ibukeev/cat_bike/docs/design/photo-layout-analysis.md

# Photo Layout Analysis

## Purpose

Use the front/back bike photos as the baseline for LED placement, mechanical clearance, and future sculptural planning.

## Photo Reference Map

| Photo | Best Use |
|---|---|
| [01-bike-front-straight.jpg](../../assets/photos/Original_bike/front_back/01-bike-front-straight.jpg) | Front symmetry, fork clearance, tire/headlight alignment, handlebar width. |
| [02-bike-side-profile-wide.jpg](../../assets/photos/Original_bike/front_back/02-bike-side-profile-wide.jpg) | Whole-bike side layout, frame tube runs, battery clearance, pedal/chain clearance. |
| [03-bike-rear-rack-left-closeup.jpg](../../assets/photos/Original_bike/front_back/03-bike-rear-rack-left-closeup.jpg) | Rear rack, basket attachment, left-side tail mount options. |
| [04-bike-rear-straight.jpg](../../assets/photos/Original_bike/front_back/04-bike-rear-straight.jpg) | Rear visibility, tail symmetry, basket rear face, rear tire clearance. |
| [05-bike-side-profile-close.jpg](../../assets/photos/Original_bike/front_back/05-bike-side-profile-close.jpg) | Main side-frame LED routes and panel candidate zones. |
| [06-bike-rear-three-quarter-close.jpg](../../assets/photos/Original_bike/front_back/06-bike-rear-three-quarter-close.jpg) | Rear rack, basket side, tail path, rear wiring path. |
| [07-bike-rear-three-quarter-wide.jpg](../../assets/photos/Original_bike/front_back/07-bike-rear-three-quarter-wide.jpg) | Whole-bike rear/side silhouette and visibility from distance. |
| [08-bike-front-top-handlebar-head-tube.jpg](../../assets/photos/Original_bike/front_back/08-bike-front-top-handlebar-head-tube.jpg) | Handlebar/head tube area, head mount envelope, brake cable and headlight clearance. |

## First-Pass Layout Annotations

### Front Area

- The existing front headlight sits low and forward; do not block it unless it is intentionally replaced.
- The handlebar and head tube area are crowded with brake cables and controls, so the cat head should either mount to a dedicated bracket or use a carefully placed handlebar/stem clamp.
- Front fork lighting can run down the fork legs, but must stay clear of the tire, brake rotor, and cable motion.
- The cat head should be removable and should have a service connector near the head tube or stem.

### Side Frame

- The lower frame tube is the strongest candidate for Phase 1 underglow because it is independent of future sculptural panels.
- The large battery occupies the central frame area; do not block battery removal, key access, or charging access.
- The step-through frame creates a good visible side silhouette, but panel work should remain removable.
- Pedal, chain, and kickstand clearance should be treated as no-go zones for wiring and panels.

### Rear Rack and Basket

- The rear rack and basket provide strong mounting structure for Phase 1 rear lighting.
- Basket perimeter lighting is useful for rear/side visibility and does not depend on body panels.
- Tail mounting should use the rack/basket structure, with a quick disconnect and a secondary safety tether.
- Tail design must preserve cargo use unless cargo is intentionally sacrificed for the event build.

### Body Panels

- Body panels should be treated as Phase 3 because LED placement may depend on the inside face of the panel.
- Phase 1 should reserve power/data connectors for future panel lighting instead of installing those LEDs early.
- Candidate panel zones are the side frame opening, rear rack side, and front lower frame/fork transition.

### Wheels

- Wheel effects remain Phase 4. They are visually strong but add durability, power, and maintenance complexity.
- Any wheel lighting must avoid spokes, brake rotors, tires, valve stems, and wheel removal/service.

## Phase 1 Reference Review

Current visual reference: [phase1-led-reference-v3-current.png](../../assets/photos/Concepts/Bio-Luminescent%20Abyssinian/Phase_1_LED_References/phase1-led-reference-v3-current.png)

What to keep:

- Restrained lower frame lighting with a segmented addressable feel.
- Short fork accents instead of full fork outlines.
- Rear rack support accents.
- Subtle hidden basket underside glow.
- Soft ground underglow.
- Cyan/aqua base palette with small violet/magenta pulse accents.
- Unlit flag post.

What to reject from earlier iterations:

- Wheel rings, tire lights, spoke lights, and wheel effects.
- Handlebar, grip, brake lever, or control-area lighting.
- Dense basket-face lighting or woven basket string lights.
- Random magenta dots not tied to a real endpoint or junction.
- Any literal geometry that cannot be mounted cleanly with removable, protected LED channels.

## Rough Reference Dimensions

These are planning references based on current RadRunner-family specifications and should be verified against Olga's actual bike before ordering parts or cutting materials.

| Dimension | Reference Value | Planning Use |
|---|---:|---|
| Total bike length | 68 in / 172.7 cm | Overall side layout and transport envelope. |
| Wheelbase | 45 in / 114.3 cm | Scales side-view estimates. |
| Handlebar width | 27 in / 68.6 cm | Front cat head maximum visual width reference. |
| Handlebar height | 42-45 in / 106.7-114 cm | Cat head height and rider sightline reference. |
| Tire size | 20 in x 3.3 in | Fork, wheel, and fender clearance reference. |
| Rear rack payload | 120 lb / 54.4 kg | Tail/rack sculpture load reference, though the sculpture should be far lighter. |

Sources:

- Rad Power Bikes product specs: https://www.radpowerbikes.com/collections/eligible-ebikes/products/radrunner-electric-cargo-utility-bike

## Phase 1 Candidate LED Runs

| Zone | Rough Length Estimate | Why It Belongs in Phase 1 |
|---|---:|---|
| Lower frame underglow | 30-45 in per side | Independent of panels, high visibility, protected if mounted inboard. |
| Fork legs | 18-24 in per fork leg | Improves front visibility; must be mechanically protected. |
| Rear rack perimeter | 40-70 in | Strong mounting structure and rear visibility. |
| Basket front/rear faces | 30-60 in total | High visibility, easy to mount, removable with basket work. |

## Reserved Interfaces

| Future Zone | Reserve Location | Notes |
|---|---|---|
| Cat head | Head tube/stem area | Needs power/data quick disconnect and strain relief. |
| Tail | Rear rack/basket area | Needs removable connector and safety tether route. |
| Body panels | Side frame and rear rack area | Wait for real panel geometry before installing LEDs. |
| Wheels | Near fork/rear triangle only if pursued | Defer until fixed lighting is stable. |

## Measurements Still Needed

- Actual lower frame tube LED path length.
- Fork leg usable straight length.
- Rear rack and basket dimensions.
- Basket hole spacing and usable clamp locations.
- Battery removal path and required clearance.
- Headlight beam envelope.
- Full steering sweep with cables.
- Tail mount envelope and cargo clearance.
