ibukeev/cat_bike/hardware/mechanical/fabrication/templates/cat-head-wireframe-prototype/gemini_3d_plus_symmetry_report.md

# Gemini 3D Plus Symmetry Model Report

This is a proof model generated from manual mappings plus accepted symmetry-derived points. It is not fabrication-ready CAD.

## Counts

- 3D nodes: 69
- Rods generated: 162
- Skipped projection edges: 31
- Heavy-estimate nodes: 30
- Heavy-estimate nodes in inferred back/deep half: 22
- manual 3-view trace: 17
- symmetry, traced mirror nodes: 4
- manual partial constraints: 14
- some estimated projection: 4
- heavily estimated: 30

## Fit Summary

- top_x_to_front_x: x = 1.082926 * top_x + -30.919
- top_y_to_side_depth: y = -0.862602 * top_y + 3133.149
- side_y_to_front_y: z_y = 1.005460 * side_y + -5.852

## Files

- `gemini-3d-plus-symmetry-wireframe.html`
- `gemini-3d-plus-symmetry-wireframe.obj`
- `gemini-3d-plus-symmetry-wireframe.stl`
- `gemini_3d_plus_symmetry_nodes.csv`
- `gemini_3d_plus_symmetry_rods.csv`
- `gemini_obj_part_map.csv`
- `gemini_3d_plus_symmetry_projection_residuals.csv`
- `gemini_3d_plus_symmetry_skipped_edges.csv`
- `gemini-3d-back-review-markers.obj`
- `gemini-3d-back-review-markers.mtl`
- `gemini_3d_back_review_nodes.csv`
