ibukeev/cat_bike/assets/photos/Concepts/Selected/Bio-Luminescent Abyssinian/Phase_1_LED_References/body-strip-design-options-v1/generation-prompts.md

# Regeneration prompt sequence

Use built-in `image_gen`. Begin with the corrected placement mockup as the only conversation image, then use each latest result as the sole input for the next option (`num_last_images_to_include: 1`). Preserve the real bicycle, geometry, background, and dusk treatment in every edit.

## Option 1 — Minimal Feline Silhouette

`Replace the existing LED routing with exactly three elements: one continuous cyan/teal lower-frame strip following the rear lower frame through the step-through belly curve; one continuous cyan/teal upper rear haunch strip beneath the seat/rack ending under the basket; and one short downward-facing basket-underlight. Remove vertical torso strips and accents. Keep generous dark negative space.`

## Option 2 — Bioluminescent Dashes

`Replace continuous strips with 7–9 short cyan/teal segments along the lower frame and belly curve, 4–5 separated segments along the upper rear haunch, one basket-underlight, and only two short magenta accents. Maintain consistent dark gaps and an organic animal-marking rhythm.`

## Option 3 — Feline Ribcage

`Remove the dashed outline. Add one cyan upper rear spine, four short diagonal cyan ribs on removable backing bars across the fixed rear-rack triangle, one short lower sternum/belly strip, one basket-underlight, and one small magenta heartbeat accent. Leave the front half mostly dark.`

## Option 4 — Geometric Facet Echo

`Remove the ribcage. Add 6–8 straight strip strokes: 4–5 forming two incomplete angular chevrons/open facets in the fixed rear-rack triangle, two short lower-frame strokes forming a shallow forward chevron, one basket-underlight, and one short magenta facet edge. Keep gaps at every corner; use no sharply bent continuous strip.`

## Invariants for every prompt

`No LEDs on forks, wheels, tires, spokes, brake rotors, chain, crank, steering components, cables, or moving parts. No illuminated panels or cat head. No labels, arrows, text, or watermark. Show visible LED nodes and physically plausible attachment to fixed frame/rack members or narrow removable backing bars.`
