ibukeev/cat_bike/docs/PROJECT_PLAN.md

# Cat Bike LED Installation Project Plan

This is the historical planning ledger. Start at
[the fabrication index](../hardware/mechanical/fabrication/3d-print/README.md)
for retained build files. Early handlebar/cardboard mount plans were retired
on 2026-09-10; their links now point to retained build records or the later
frame-fixed mount. This does not change historical task or approval statuses.

## Priority Definitions

- `P0`: Blocking work needed to make the bike rideable, safe, and buildable.
- `P1`: Important work for the Bio-Luminescent Abyssinian identity and playa-ready experience.
- `P2`: Enhancements, showpiece upgrades, polish, and later-phase improvements.

| Workstream | Task | Priority | Task Details | Artefacts | Status |
|---|---|---:|---|---|---|
| Project Definition | Define final bike goals | P0 | Use the Bio-Luminescent Abyssinian concept as the current visual direction. The bike must be rideable and safe day/night, durable against dust/moisture/vibration, iterative, easy to disassemble after Burning Man, and extendable later. | [Concept brief](design/bio-luminescent-abyssinian-concept.md) | Done |
| Project Definition | Define build phases | P0 | Split the project into electrical and independent lighting foundation, cat head, tail, body panels with integrated LEDs, and showpiece upgrades so each phase adds standalone value. | [Concept brief](design/bio-luminescent-abyssinian-concept.md) | Done |
| Visual Design | Document Bio-Luminescent Abyssinian concept | P1 | Capture the keeper elements: gold frame base, faceted copper/rose-gold cat head, cyan/aqua/magenta glow, fiber-optic whiskers, illuminated tail, body glow, and optional wheel effects. | [Concept brief](design/bio-luminescent-abyssinian-concept.md), [Design proposal](design/design-proposal.md) | In Progress |
| Visual Design | Photograph bike for layout planning | P0 | Capture side, front, rear, and top views for annotated LED placement diagrams. | [LED zone plan](design/led-zone-plan.md), [Photo layout analysis](design/photo-layout-analysis.md) | Done |
| Visual Design | Create LED placement concept | P0 | Mark proposed LED zones: frame, fork, rear rack, basket, cat head, eyes, whiskers, tail, underglow, and optional wheels. | [LED zone plan](design/led-zone-plan.md), [Photo layout analysis](design/photo-layout-analysis.md) | Done |
| Electrical | Estimate LED count and power draw | P0 | Calculate max and typical current for selected LED type, brightness limits, and Pixelblaze output plan. Tentative decisions: 5 V primary system; 25-35% riding, 50-60% show, 10-15% reserve brightness caps. | [Power budget](../hardware/electrical/power-budget.md), [Photo layout analysis](design/photo-layout-analysis.md) | In Progress |
| Electrical | Select battery and protection | P0 | Choose dedicated LED battery voltage/capacity, fuse, switch, connectors, charging method, mounting direction, and runtime target. Do not tap or modify the bike battery. | [Power budget](../hardware/electrical/power-budget.md), [Initial parts list](bom/initial-parts-list.md) | In Progress |
| Electrical | Design wiring harness | P0 | Document wire gauges, connector types, power injection points, strain relief, service disconnects, and reserved power/data interfaces for later head, tail, panels, and optional wheels. | [Power budget](../hardware/electrical/power-budget.md), [LED zone plan](design/led-zone-plan.md), [Wiring harness architecture](../hardware/electrical/wiring/wiring-harness-architecture.md) | In Progress |
| Controller | Define Pixelblaze setup | P0 | Record controller model, pin usage, network setup, mounting location, and configuration notes. | [Pixelblaze setup](../hardware/electrical/controller-pixelblaze/pixelblaze-setup.md), [LED zone plan](design/led-zone-plan.md), [Power budget](../hardware/electrical/power-budget.md) | In Progress |
| Software | Create Pixelblaze pattern set | P1 | Build base patterns for visibility, ambient bioluminescent motion, parked/show mode, and low-power operation. | [Concept brief](design/bio-luminescent-abyssinian-concept.md), [LED zone plan](design/led-zone-plan.md) | Not Started |
| Software | Define LED segment map | P0 | Map physical LED zones to Pixelblaze indices so patterns can target bike sections predictably, especially cat head, eyes, whiskers, tail, frame, rack, and optional wheels. | [LED zone plan](design/led-zone-plan.md), [Pixelblaze setup](../hardware/electrical/controller-pixelblaze/pixelblaze-setup.md) | In Progress |
| Mechanical | Plan mounts and enclosures | P0 | Choose mounting method for LEDs, battery, controller, wiring, and weather/dust protection. Prioritize serviceable, removable parts for playa repair. | [Power enclosure plan](../hardware/mechanical/enclosures/power-enclosure-plan.md), [LED diffuser and mounting plan](../hardware/mechanical/mounts/led-diffuser-mounting-plan.md), [Frame-fixed aluminum mount](../hardware/mechanical/fabrication/metal/cat-head-frame-fixed-mount-v0/README.md), [Initial parts list](bom/initial-parts-list.md) | In Progress |
| Mechanical | Phase 2A cat head MVP | P1 | Build the minimum removable cat head prototype and temporary support system needed to test scale, faceted finish, whiskers, lighting fit, steering clearance, and mount behavior. Current status: V1 wireframe shape/topology is frozen; next MVP step is cardboard panel prototyping from the V1 node/rod graph. | [Design proposal](design/design-proposal.md), [Retained head prototypes and build files](../hardware/mechanical/fabrication/3d-print/README.md), [Cat head wireframe plan](design/cat-head-verified-rods-plan.md), [V1 wireframe snapshot](../hardware/mechanical/fabrication/templates/cat-head-wireframe-prototype/versions/v1-shape-approved-cardboard-prototype/README.md), [Frame-fixed aluminum mount](../hardware/mechanical/fabrication/metal/cat-head-frame-fixed-mount-v0/README.md), [Cat head lighting plan](../hardware/electrical/leds/cat-head-lighting-plan.md) | In Progress |
| Mechanical | Phase 2A cat head design | P1 | Design the removable cat head module: daytime gold/mirror faceted identity, semi-transparent glow panels, eyes, fiber-optic whiskers, internal LED layout, quick disconnect, and mount envelope. Current design direction: rod/wireframe skeleton plus flat cardboard panels for the next prototype; later material candidates include gold mirror vinyl over thin panels, mirrored plastic, and frosted/smoked translucent diffuser panels. | [Design proposal](design/design-proposal.md), [Retained head prototypes and build files](../hardware/mechanical/fabrication/3d-print/README.md), [Cat head wireframe plan](design/cat-head-verified-rods-plan.md), [Active wireframe prototype workspace](../hardware/mechanical/fabrication/templates/cat-head-wireframe-prototype/README.md), [Frame-fixed aluminum mount](../hardware/mechanical/fabrication/metal/cat-head-frame-fixed-mount-v0/README.md), [Cat head lighting plan](../hardware/electrical/leds/cat-head-lighting-plan.md), [Concept brief](design/bio-luminescent-abyssinian-concept.md), [Pixelblaze setup](../hardware/electrical/controller-pixelblaze/pixelblaze-setup.md) | In Progress |
| Mechanical | Freeze cat head wireframe V1 | P1 | Preserve the current approved wireframe state as a named baseline before generating cardboard panel templates or continuing topology edits. Snapshot includes OBJ/STL/HTML, node and rod CSVs, reports, and source generator inputs. | [V1 wireframe snapshot](../hardware/mechanical/fabrication/templates/cat-head-wireframe-prototype/versions/v1-shape-approved-cardboard-prototype/README.md) | Done |
| Mechanical | Generate cardboard panel prototype | P1 | Use the V1 wireframe graph to choose panel faces, generate labeled flat cardboard templates, and build a taped faceted shell quickly to validate silhouette, scale, and assembly before final materials. | [V1 wireframe snapshot](../hardware/mechanical/fabrication/templates/cat-head-wireframe-prototype/versions/v1-shape-approved-cardboard-prototype/README.md), [Cat head wireframe plan](design/cat-head-verified-rods-plan.md) | Not Started |
| Mechanical | Plan cat head mount | P0 | Design a front cat head/mask mount that does not block steering, brake cables, rider sightline, or the existing headlight. | [Frame-fixed aluminum mount](../hardware/mechanical/fabrication/metal/cat-head-frame-fixed-mount-v0/README.md) | In Progress |
| Mechanical | Plan tail mount | P1 | Design a lightweight illuminated tail mounted to the rear rack or basket area, with independent quick-disconnect wiring and clearance for cargo and rider movement. | [Concept brief](design/bio-luminescent-abyssinian-concept.md), [Initial parts list](bom/initial-parts-list.md) | In Progress |
| BOM | Build parts list | P0 | Track LEDs, battery, controller, wires, connectors, fuses, mounts, adhesives, tools, and spares. | [Initial parts list](bom/initial-parts-list.md) | In Progress |
| Safety | Define safety checklist | P0 | Include fuse check, insulation, strain relief, charging safety, heat checks, and emergency disconnect. | [Power budget](../hardware/electrical/power-budget.md), [Frame-fixed aluminum mount](../hardware/mechanical/fabrication/metal/cat-head-frame-fixed-mount-v0/README.md) | Not Started |
| Safety | Check ride clearance | P0 | Verify sculpture, whiskers, tail, wiring, and LED mounts do not interfere with pedaling, steering, braking, tires, chain, rider clothing, or cargo. | [Frame-fixed aluminum mount](../hardware/mechanical/fabrication/metal/cat-head-frame-fixed-mount-v0/README.md), [LED zone plan](design/led-zone-plan.md), [Photo layout analysis](design/photo-layout-analysis.md) | Not Started |
| Testing | Bench test electronics | P0 | Test controller, LEDs, wiring, current draw, brightness limits, and runtime before bike installation. | [Power budget](../hardware/electrical/power-budget.md) | Not Started |
| Testing | Bike installation test | P0 | Verify mounting security, steering clearance, wheel clearance, vibration resistance, and cable routing. | [Frame-fixed aluminum mount](../hardware/mechanical/fabrication/metal/cat-head-frame-fixed-mount-v0/README.md), [LED zone plan](design/led-zone-plan.md) | Not Started |
| Testing | Night visibility test | P1 | Check appearance, brightness, visibility angles, power draw, and pattern readability outdoors at night. | [Concept brief](design/bio-luminescent-abyssinian-concept.md), [LED zone plan](design/led-zone-plan.md) | Not Started |
| Playa Readiness | Prepare repair kit | P1 | List spare LEDs, wire, connectors, fuses, tape, zip ties, tools, and backup power components. | [Initial parts list](bom/initial-parts-list.md) | Not Started |
| Documentation | Document final build | P2 | Add photos, wiring diagrams, BOM updates, Pixelblaze notes, and lessons learned. | [Concept brief](design/bio-luminescent-abyssinian-concept.md), [LED zone plan](design/led-zone-plan.md), [Power budget](../hardware/electrical/power-budget.md), [Frame-fixed aluminum mount](../hardware/mechanical/fabrication/metal/cat-head-frame-fixed-mount-v0/README.md), [Initial parts list](bom/initial-parts-list.md) | Not Started |
