ibukeev/cat_bike/docs/cleanup/2026-09-10/README.md

# Archive retirement record — 2026-09-10

The user authorized permanent deletion of _archive_admin/ and .cleanup-recovery/.

Current status: _archive_admin/ was permanently deleted (946 files,
5,399,146,082 regular-file bytes). Retained worktree hashes were verified before
and after deletion. The rejected generated outputs are no longer recoverable
from this working tree; existing tracked source history and its archive branch remain.

.cleanup-recovery/ was then permanently deleted after the user explicitly
approved the GitHub destination and payload and the independent download passed.
Both archive roots are absent: 956 files removed, 7,474,979,380 regular-file bytes
and 7,478,525,952 allocated bytes (about 6.97 GiB). Local Git/LFS storage remains.

## Verified retained-file backup

- Repository/branch: ibukeev/cat_bike, main.
- Initial checkpoint: 8a49229b7fe511f7f276a3dd46bb32a0622efb8a.
- Verified backup: bd84d8449205c2828a92f32adfedc204fe48b4f8, including the
  LFS attribute correction for four compact OBJ templates stored in ordinary Git.
- A fresh network clone plus Git LFS pull reproduced all 952 tracked files/links
  byte-for-byte, including 209 CAD/print paths / 187 unique LFS objects and all
  167 selected large-head geometry files.
- Git LFS fsck passed. The 17 focused Python tests and mapper/all 10 lighting
  patterns also passed inside that independent checkout.
- The exact 10-file recovery inventory and retained-file preservation checks
  passed before deletion; retained files were checked again afterward.

The backup contains retained work, not either deleted archive payload. At that
checkpoint the remaining untracked historical tests were intentionally excluded;
the separately authorized follow-up below resolves them. Existing Git history was
not rewritten. The broad historical test suite is not claimed to pass.

## Follow-up: untracked-file triage

The user subsequently authorized deleting or committing the 29 untracked tests
and root probe marker. Twenty-four tests with retained source/contracts were
selected for commit unchanged. One exact duplicate and four stale tests expecting
now-rejected eye designs to be accepted were permanently deleted, along with the
temporary marker. This did not change CAD source, geometry, approval flags, numeric
gates, or rejection/hash guards. The original file hashes remain in the retirement
inventory; it is a historical snapshot, not a promise that those deleted tests exist.

See [the test guide](../../../tests/README.md) for the exact removal rationale,
35 passing focused checks, all 10 passing lighting patterns and the remaining
full-suite failures. No backup copy of the obsolete untracked tests was created;
the duplicate's content remains in the retained V2 test.

The three original cleanup manifests and the rejected-output checkpoint are
preserved here byte-for-byte for provenance. They describe historical snapshots;
their whole-repository verification commands are obsolete after archive retirement.
Inventories and hashes do not contain the deleted geometry and cannot restore it.

Current build entry points remain in the repository README and retained fabrication
packages. No CAD geometry, design dimensions, approval or generation pins changed.
The separate Git archive branch and existing Git history are not being deleted.

The adjacent archive-retirement.json records the exact deletion targets, preserved
file hashes, verified backup scope and completed permanent deletion of both archives.
