ibukeev/cat_bike/assets/photos/Concepts/Other/16-Bit Nyan Astro-Cat/Gemini_Generated_Image_62l1nt62l1nt62l1.png

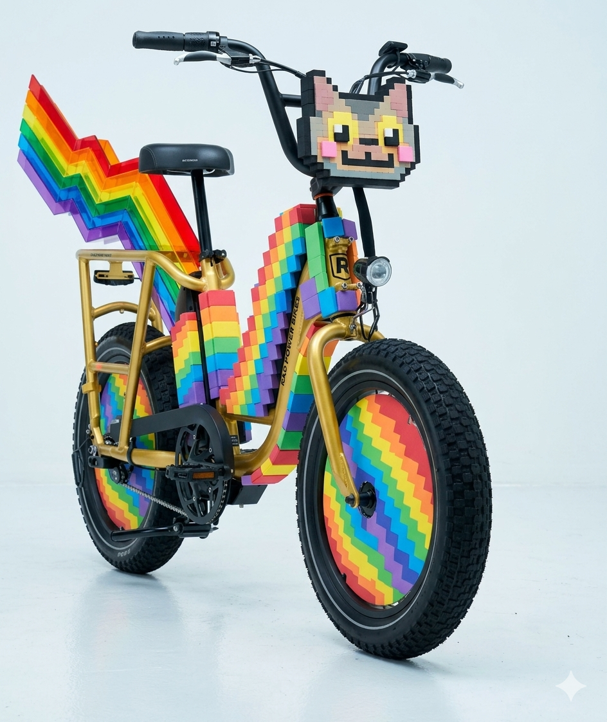
assets/photos/Concepts/Other/16-Bit Nyan Astro-Cat/Gemini_Generated_Image_62l1nt62l1nt62l1.png
