ibukeev/cat_bike/assets/photos/Concepts/Other/Galactic Tiger/Gemini_Generated_Image_chjov2chjov2chjo.png

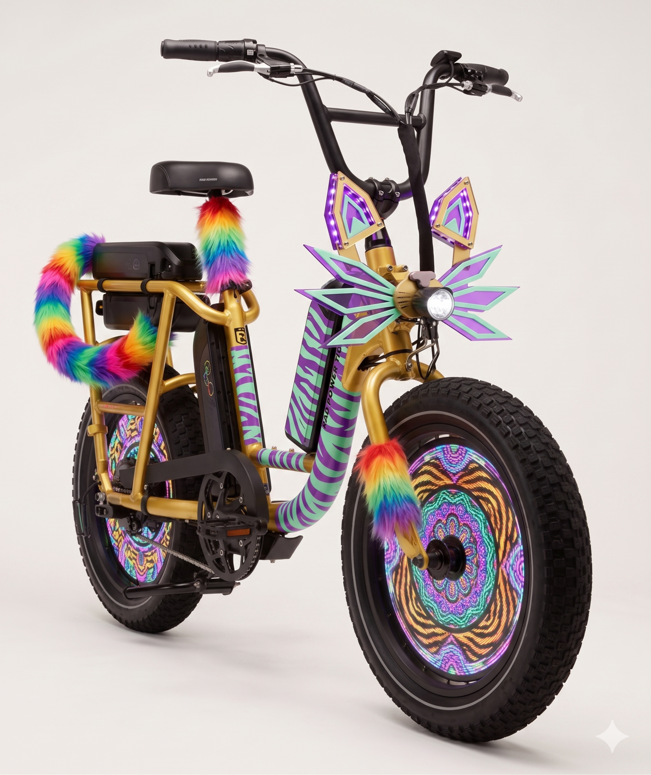
assets/photos/Concepts/Other/Galactic Tiger/Gemini_Generated_Image_chjov2chjov2chjo.png
