ibukeev/cat_bike/assets/photos/Concepts/Other/Golden Cheshire Tabby/V2/Gemini_Generated_Image_hr6m9uhr6m9uhr6m.png

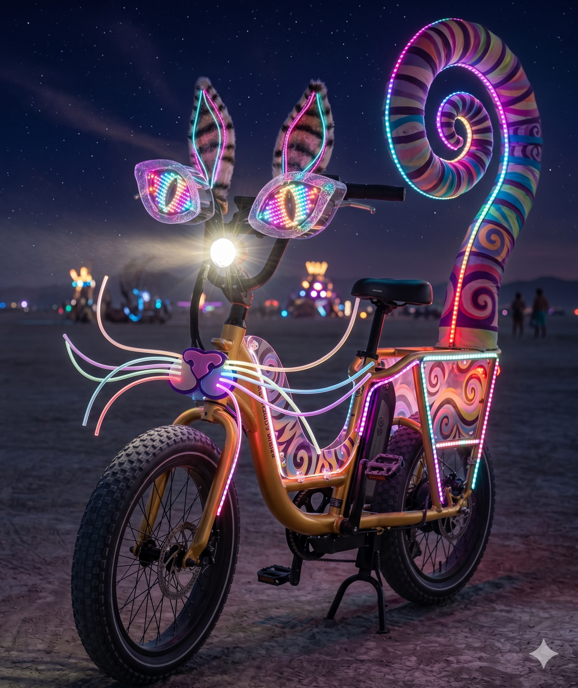
assets/photos/Concepts/Other/Golden Cheshire Tabby/V2/Gemini_Generated_Image_hr6m9uhr6m9uhr6m.png
