ibukeev/cat_bike/assets/photos/Concepts/Other/Golden Cheshire Tabby/V2/Gemini_Generated_Image_vw4zc9vw4zc9vw4z.png

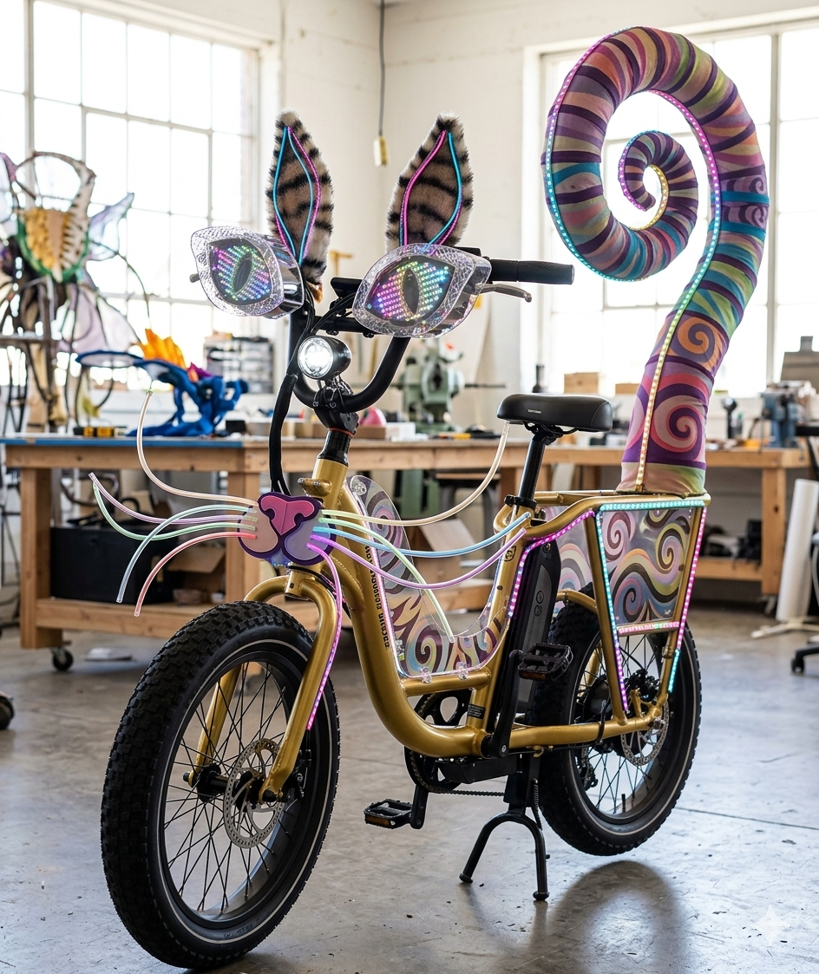
assets/photos/Concepts/Other/Golden Cheshire Tabby/V2/Gemini_Generated_Image_vw4zc9vw4zc9vw4z.png
