ibukeev/cat_bike/assets/photos/Concepts/Other/Solar Sphinx/Gemini_Generated_Image_i8vhkri8vhkri8vh.png

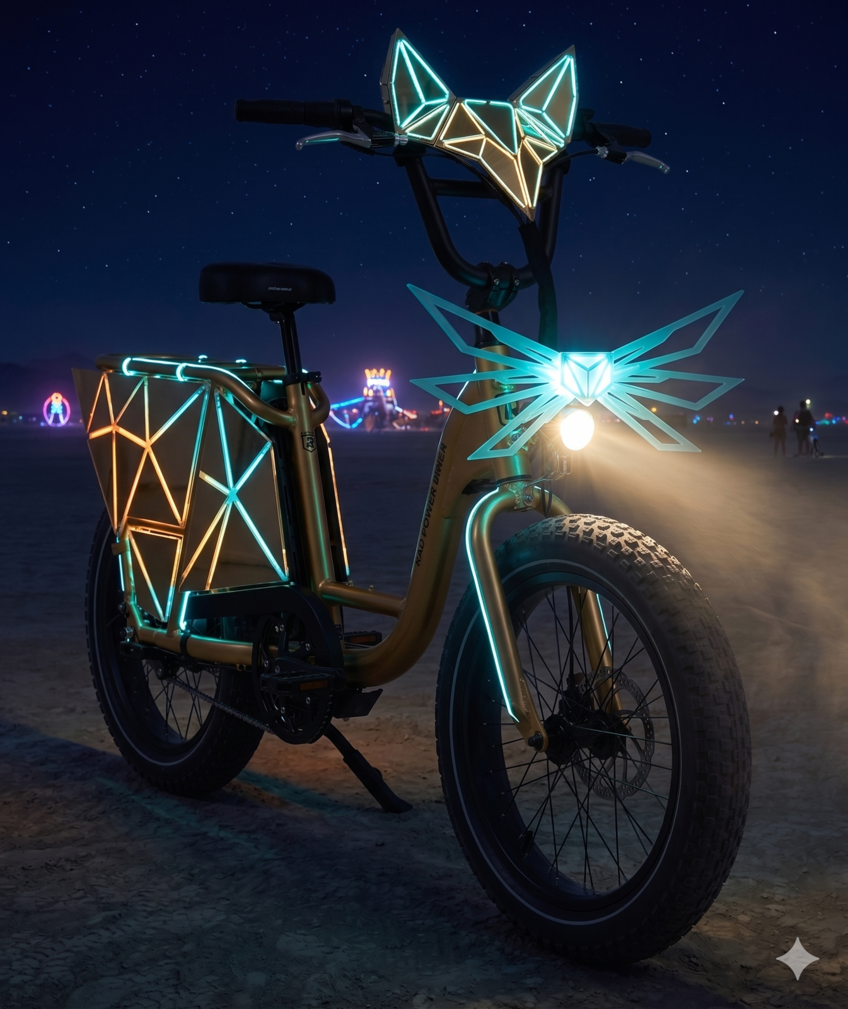
assets/photos/Concepts/Other/Solar Sphinx/Gemini_Generated_Image_i8vhkri8vhkri8vh.png
