ibukeev/cat_bike/assets/photos/Concepts/Other/Solar Sphinx/Gemini_Generated_Image_ubvsjuubvsjuubvs.png

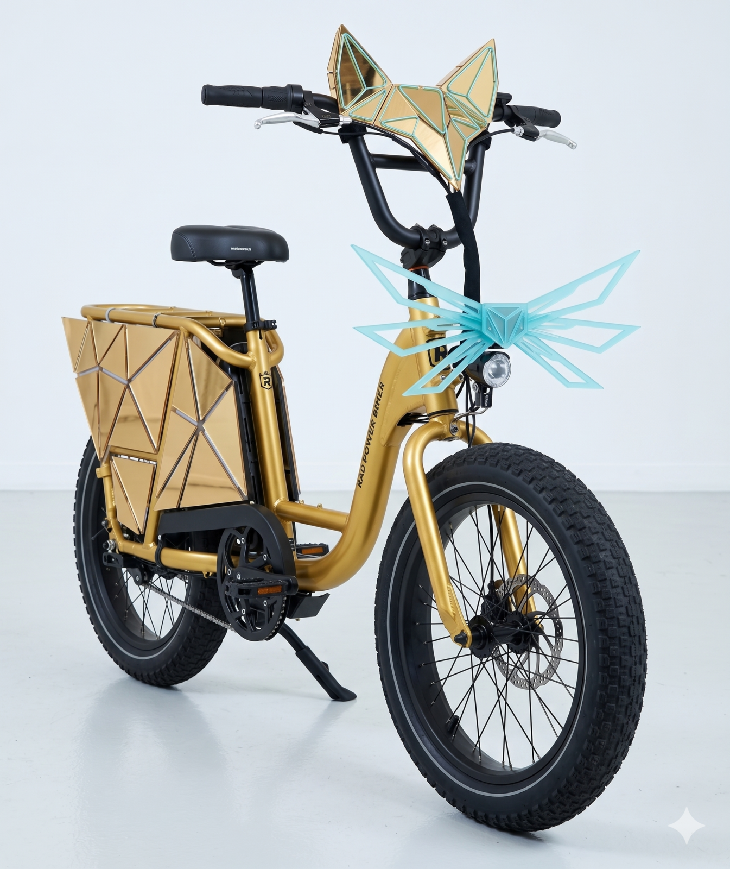
assets/photos/Concepts/Other/Solar Sphinx/Gemini_Generated_Image_ubvsjuubvsjuubvs.png
