ibukeev/cat_bike/assets/photos/Concepts/Other/The Cheshire Cloud/Gemini_Generated_Image_jn3le3jn3le3jn3l.png

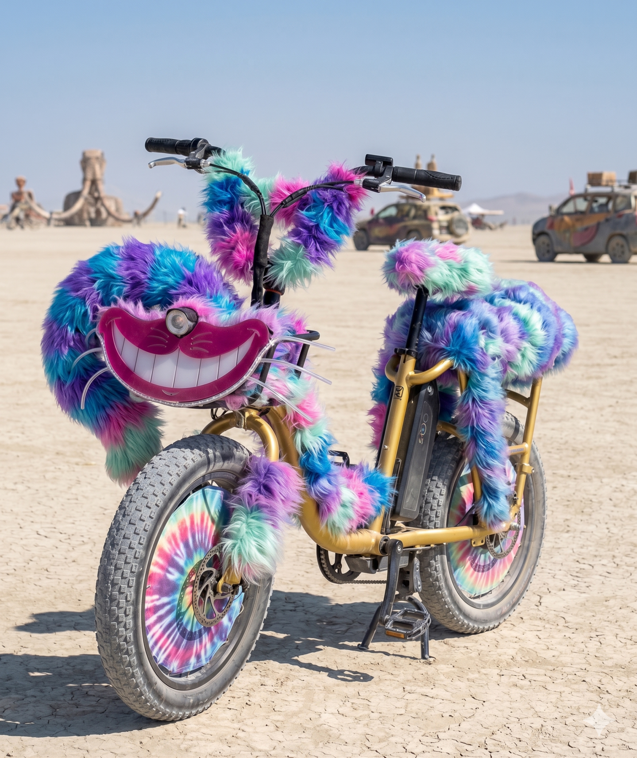
assets/photos/Concepts/Other/The Cheshire Cloud/Gemini_Generated_Image_jn3le3jn3le3jn3l.png
