ibukeev/cat_bike/assets/photos/Concepts/Other/The Cheshire Cloud/Gemini_Generated_Image_krhmmdkrhmmdkrhm.png

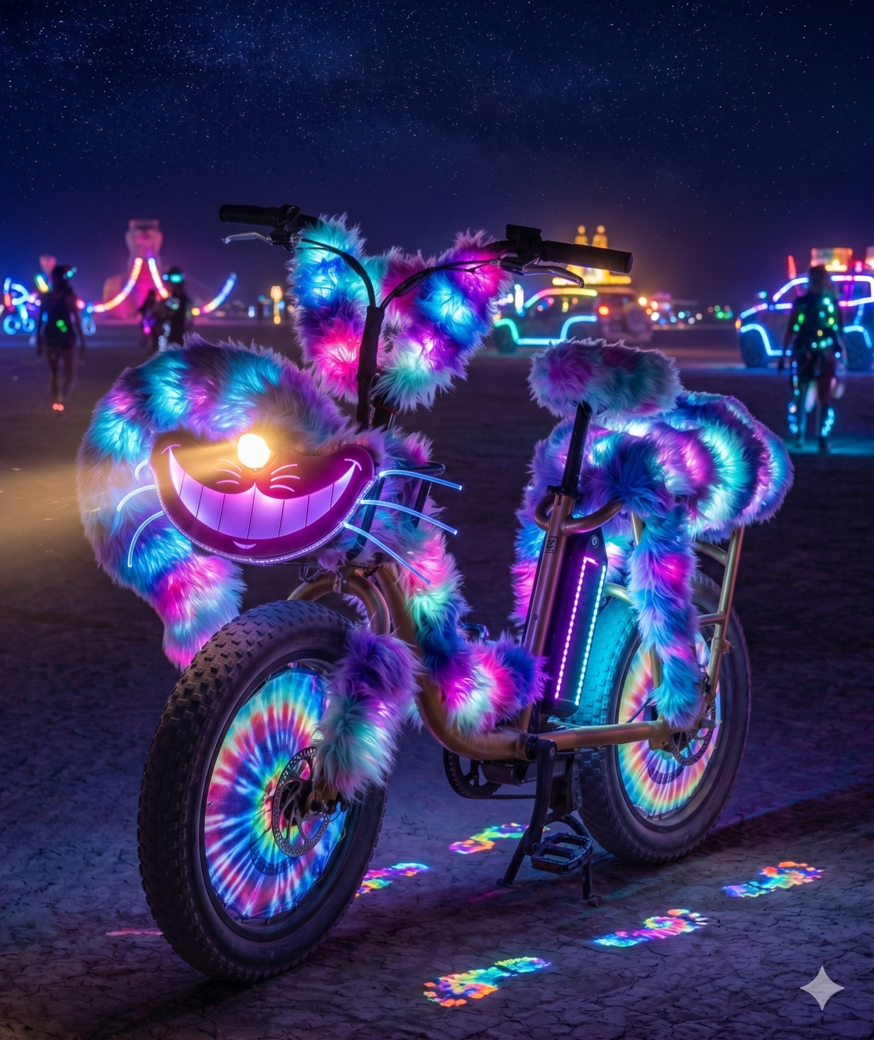
assets/photos/Concepts/Other/The Cheshire Cloud/Gemini_Generated_Image_krhmmdkrhmmdkrhm.png
