ibukeev/cat_bike/assets/photos/Concepts/Other/The Psychedelic Pallas’s Cat/Gemini_Generated_Image_pkilhwpkilhwpkil.png

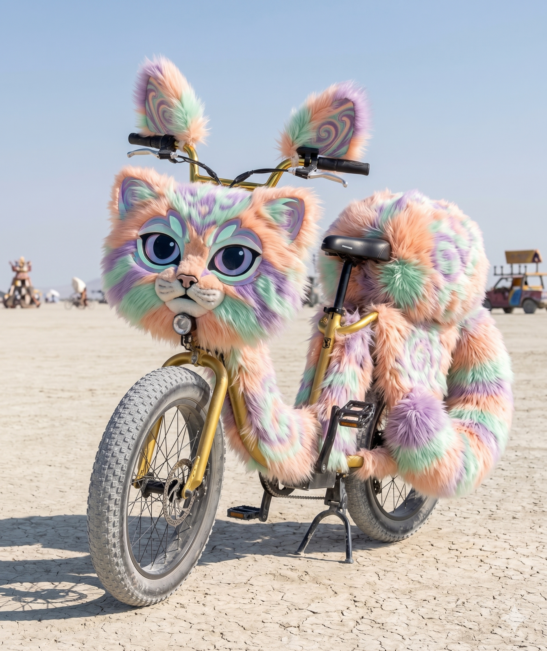
assets/photos/Concepts/Other/The Psychedelic Pallas’s Cat/Gemini_Generated_Image_pkilhwpkilhwpkil.png
