ibukeev/cat_bike/assets/photos/Concepts/Other/The Psychedelic Pallas’s Cat/Gemini_Generated_Image_zc26tdzc26tdzc26.png

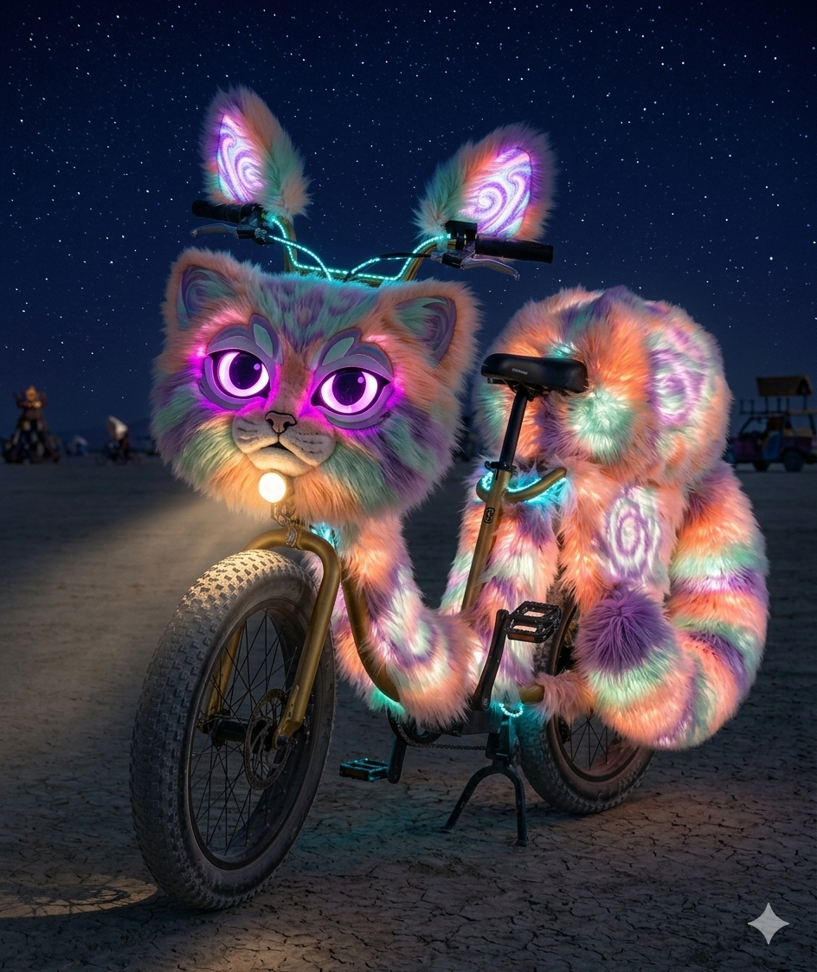
assets/photos/Concepts/Other/The Psychedelic Pallas’s Cat/Gemini_Generated_Image_zc26tdzc26tdzc26.png
