ibukeev/cat_bike/assets/photos/Concepts/Other/Victorian Steampunk/Gemini_Generated_Image_6dldgh6dldgh6dld.png

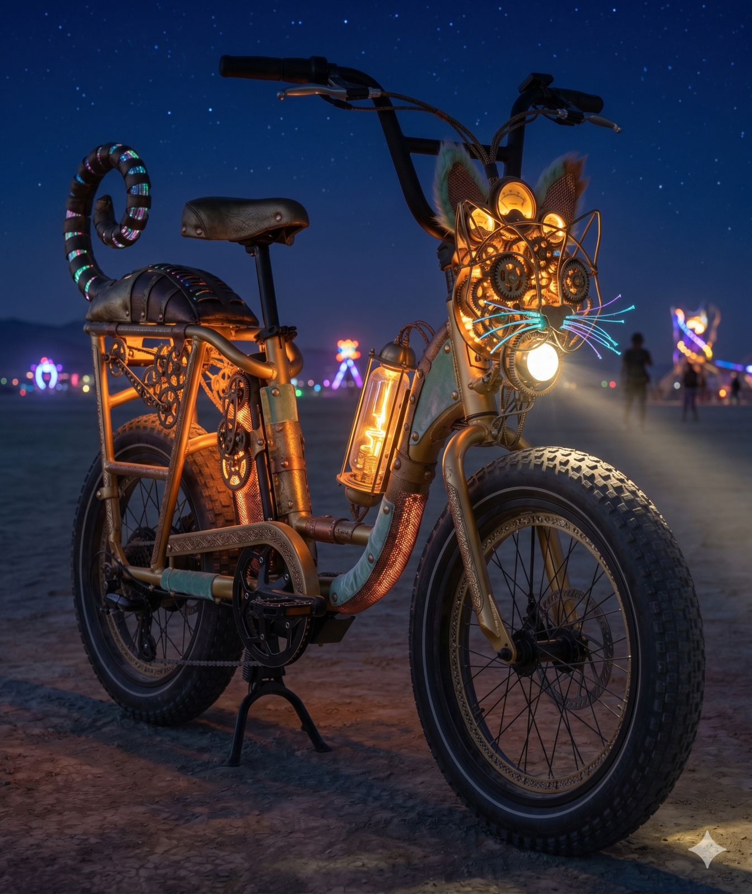
assets/photos/Concepts/Other/Victorian Steampunk/Gemini_Generated_Image_6dldgh6dldgh6dld.png
