ibukeev/cat_bike/assets/photos/Concepts/Other/Victorian Steampunk/Gemini_Generated_Image_gbmnqngbmnqngbmn.png

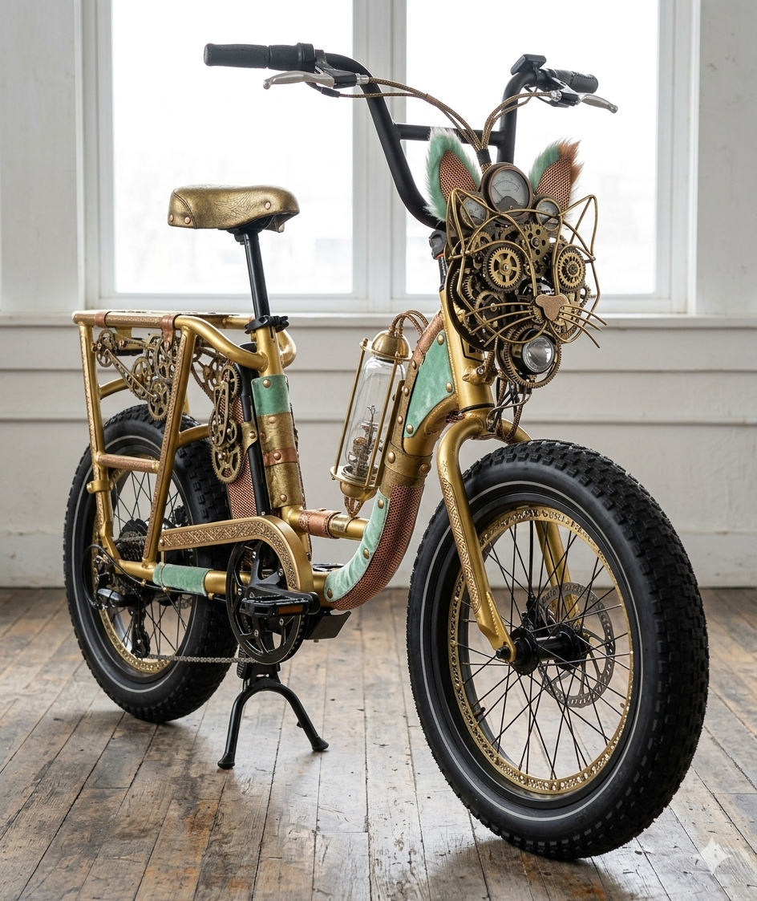
assets/photos/Concepts/Other/Victorian Steampunk/Gemini_Generated_Image_gbmnqngbmnqngbmn.png
