ibukeev/cat_bike/assets/photos/Concepts/Selected/Bio-Luminescent Abyssinian/Gemini_Generated_Image_5en5a65en5a65en5.png

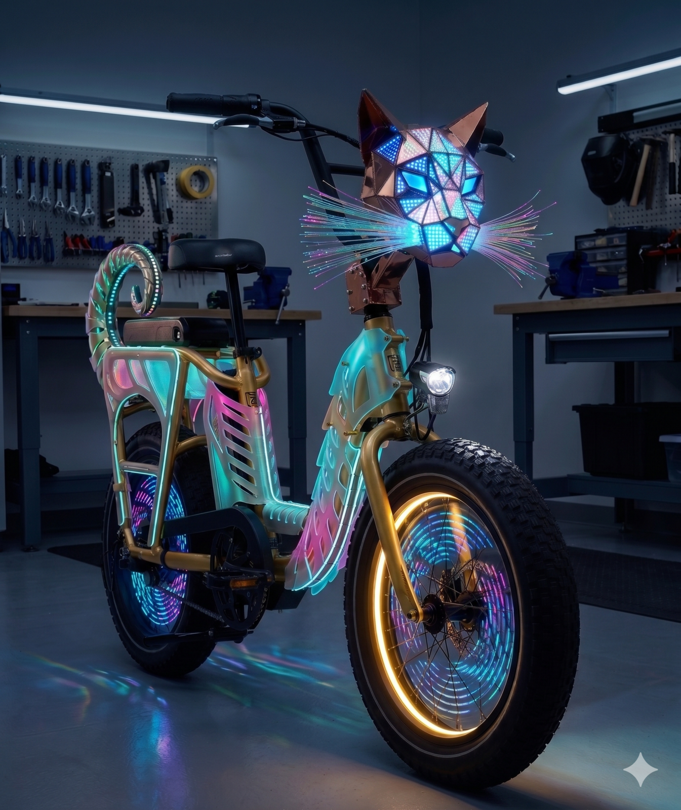
assets/photos/Concepts/Selected/Bio-Luminescent Abyssinian/Gemini_Generated_Image_5en5a65en5a65en5.png
