ibukeev/cat_bike/assets/photos/Concepts/Selected/Bio-Luminescent Abyssinian/Gemini_Generated_Image_p5pltlp5pltlp5pl.png

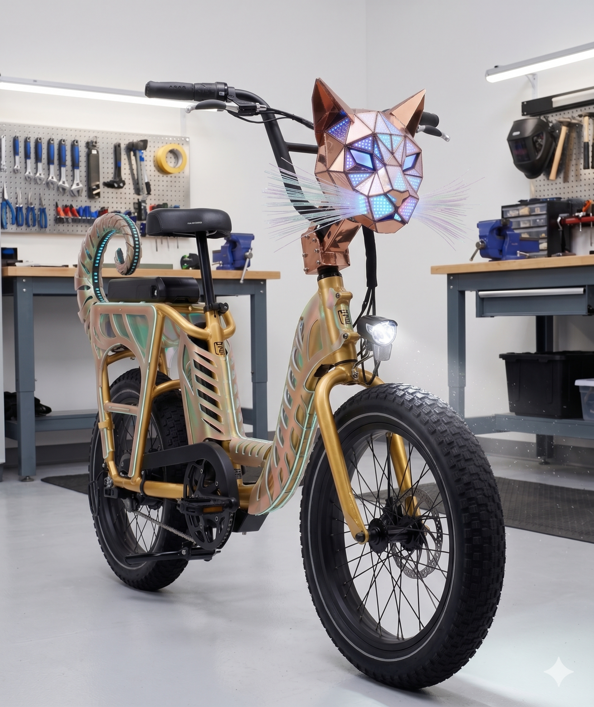
assets/photos/Concepts/Selected/Bio-Luminescent Abyssinian/Gemini_Generated_Image_p5pltlp5pltlp5pl.png
