ibukeev/cat_bike/assets/photos/Concepts/Selected/Bio-Luminescent Abyssinian/Gemini_Generated_Image_qpk2tuqpk2tuqpk2.png

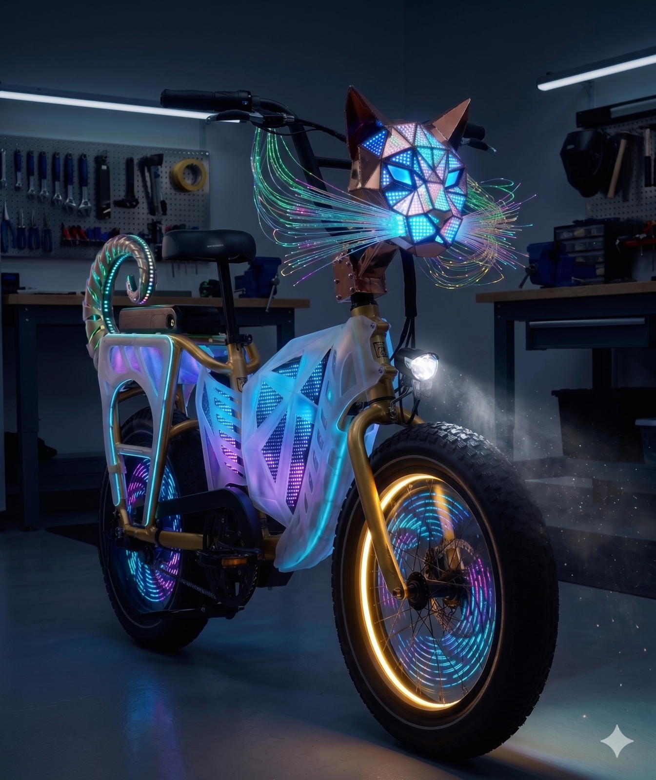
assets/photos/Concepts/Selected/Bio-Luminescent Abyssinian/Gemini_Generated_Image_qpk2tuqpk2tuqpk2.png
