ibukeev/cat_bike/assets/photos/Concepts/Selected/Bio-Luminescent Abyssinian/Gemini_Generated_Image_uw3o4uuw3o4uuw3o.png

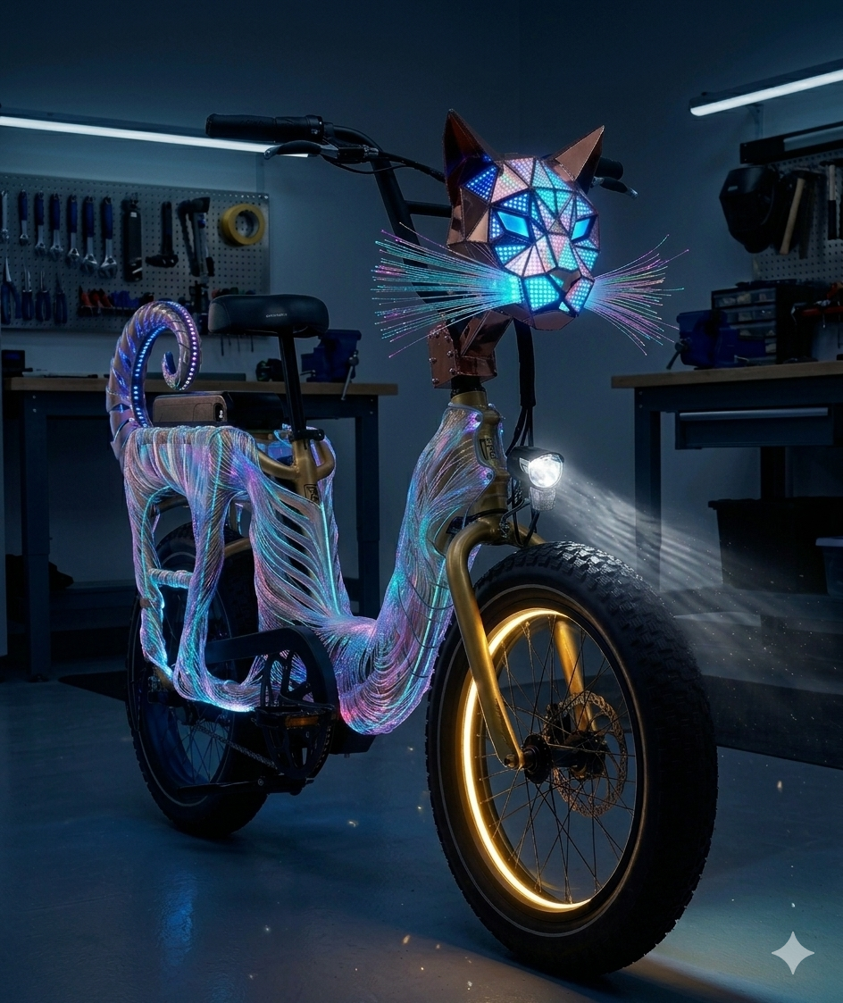
assets/photos/Concepts/Selected/Bio-Luminescent Abyssinian/Gemini_Generated_Image_uw3o4uuw3o4uuw3o.png
