ibukeev/cat_bike/assets/photos/Concepts/Selected/Bio-Luminescent Abyssinian/Iterations/ChatGPT Image May 10, 2026, 11_16_23 PM.png

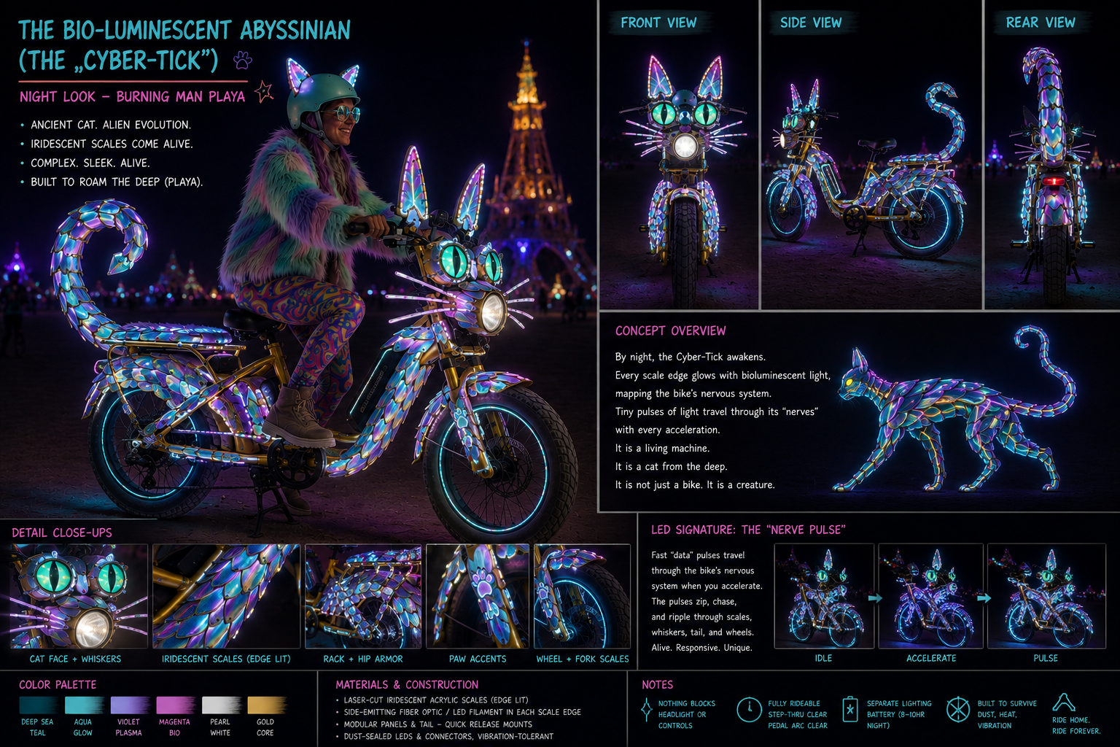
assets/photos/Concepts/Selected/Bio-Luminescent Abyssinian/Iterations/ChatGPT Image May 10, 2026, 11_16_23 PM.png
