ibukeev/cat_bike/assets/photos/Concepts/Selected/Bio-Luminescent Abyssinian/Iterations/Gemini_Generated_Image_c9wpp4c9wpp4c9wp.png

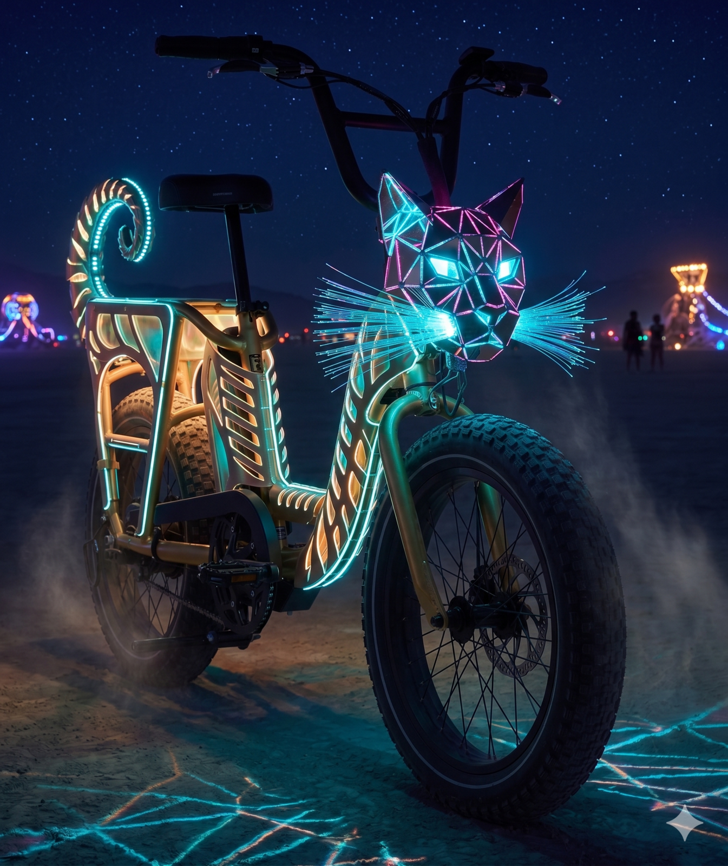
assets/photos/Concepts/Selected/Bio-Luminescent Abyssinian/Iterations/Gemini_Generated_Image_c9wpp4c9wpp4c9wp.png
