ibukeev/cat_bike/assets/photos/Concepts/Selected/Bio-Luminescent Abyssinian/Iterations/Gemini_Generated_Image_pi46pzpi46pzpi46.png

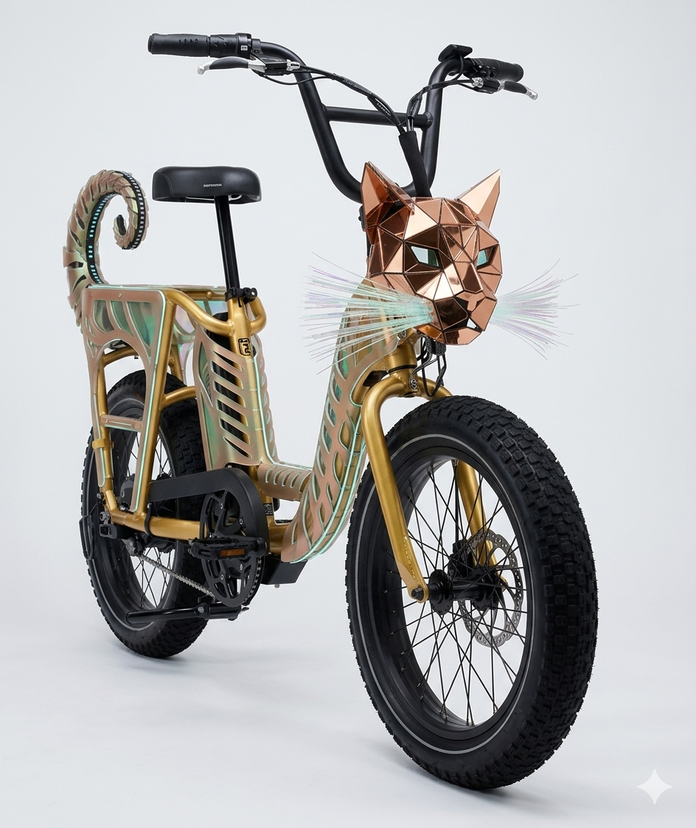
assets/photos/Concepts/Selected/Bio-Luminescent Abyssinian/Iterations/Gemini_Generated_Image_pi46pzpi46pzpi46.png
