ibukeev/cat_bike/assets/photos/Concepts/Selected/Bio-Luminescent Abyssinian/Phase_1_LED_References/body-strip-design-options-v1/01-minimal-feline-silhouette.png

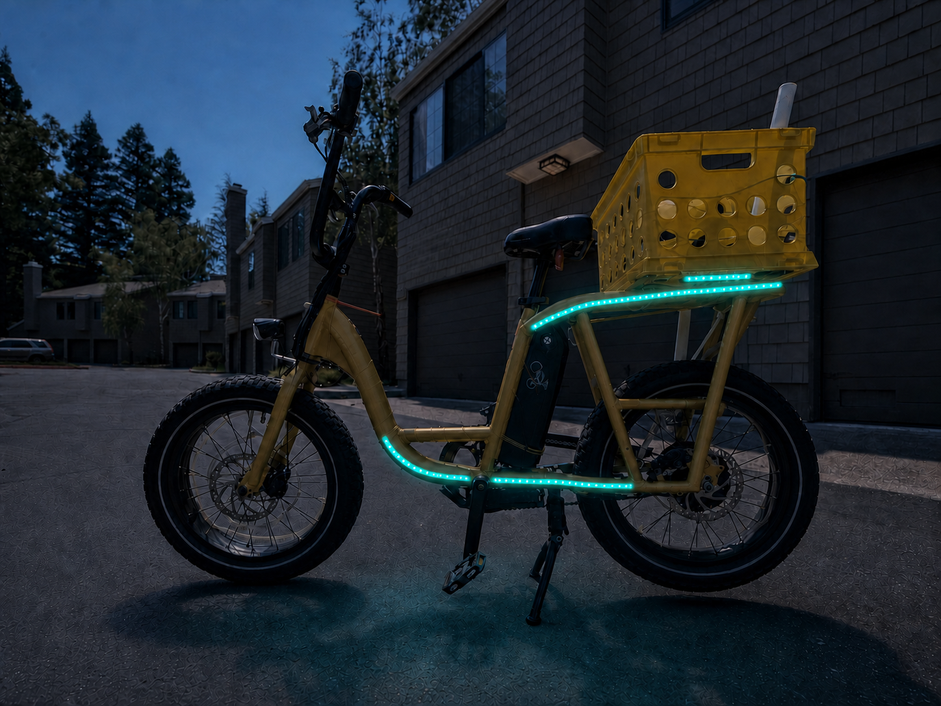
assets/photos/Concepts/Selected/Bio-Luminescent Abyssinian/Phase_1_LED_References/body-strip-design-options-v1/01-minimal-feline-silhouette.png
