ibukeev/cat_bike/assets/photos/Concepts/Selected/Bio-Luminescent Abyssinian/Phase_1_LED_References/body-strip-design-options-v1/03-feline-ribcage.png

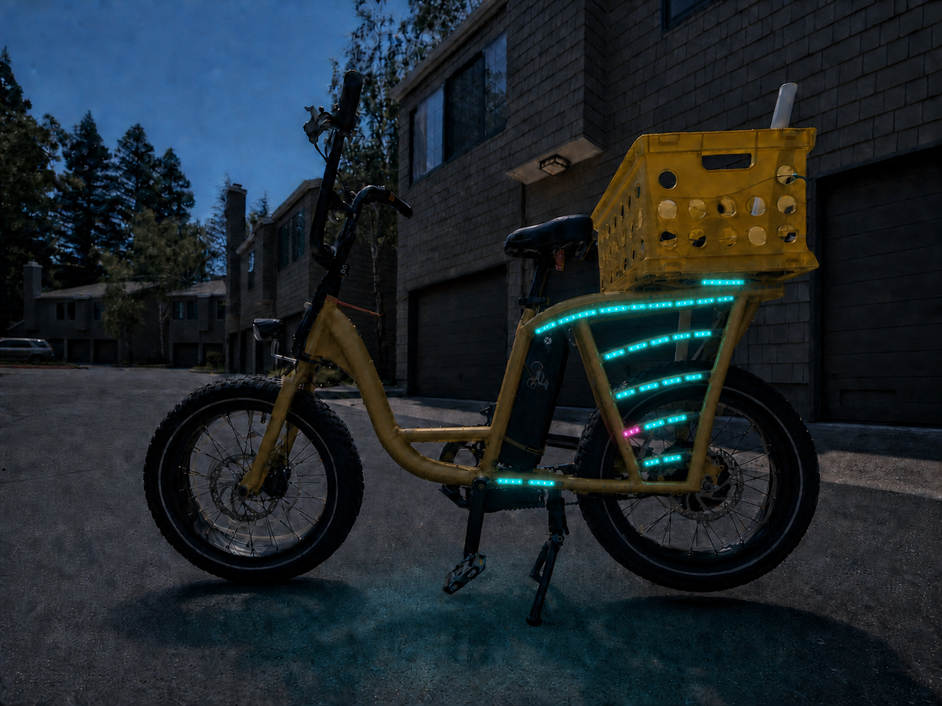
assets/photos/Concepts/Selected/Bio-Luminescent Abyssinian/Phase_1_LED_References/body-strip-design-options-v1/03-feline-ribcage.png
