ibukeev/cat_bike/assets/photos/Concepts/Selected/Bio-Luminescent Abyssinian/Phase_1_LED_References/phase1-led-reference-v1-too-busy.png

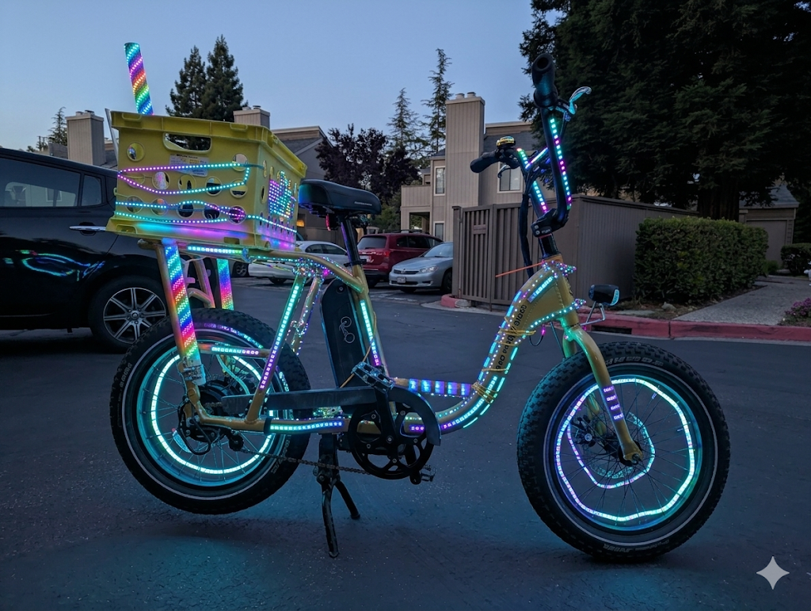
assets/photos/Concepts/Selected/Bio-Luminescent Abyssinian/Phase_1_LED_References/phase1-led-reference-v1-too-busy.png
