ibukeev/cat_bike/assets/photos/Concepts/Selected/Bio-Luminescent Abyssinian/Phase_1_LED_References/phase1-led-reference-v2-simplified.png

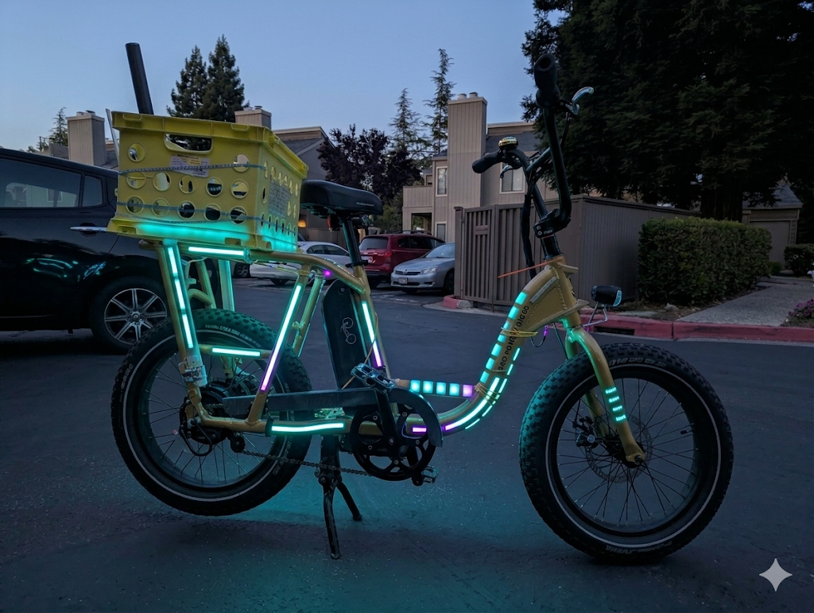
assets/photos/Concepts/Selected/Bio-Luminescent Abyssinian/Phase_1_LED_References/phase1-led-reference-v2-simplified.png
