ibukeev/cat_bike/assets/photos/Original_bike/front_back/01-bike-front-straight.jpg

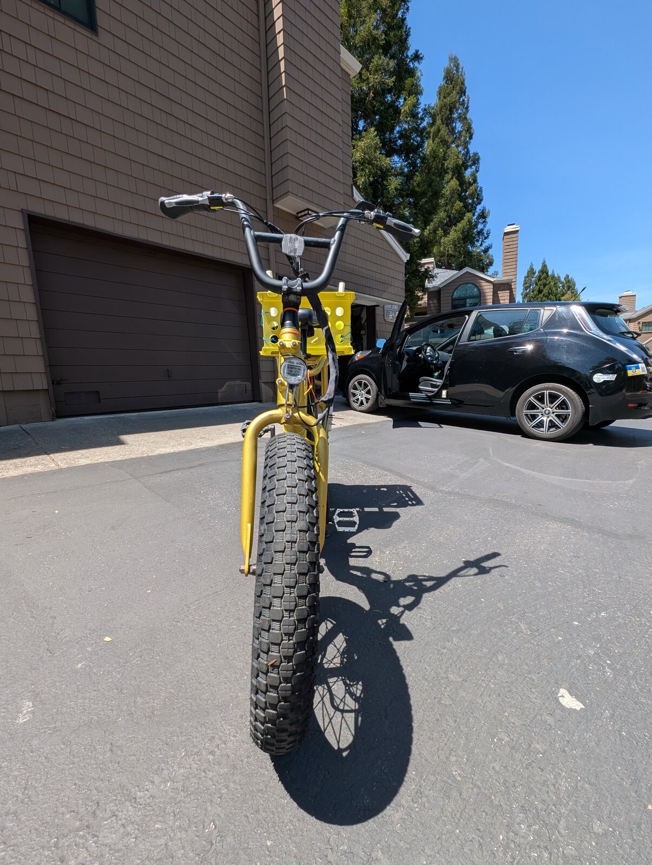
assets/photos/Original_bike/front_back/01-bike-front-straight.jpg
