ibukeev/cat_bike/assets/photos/Original_bike/front_back/02-bike-side-profile-wide.jpg

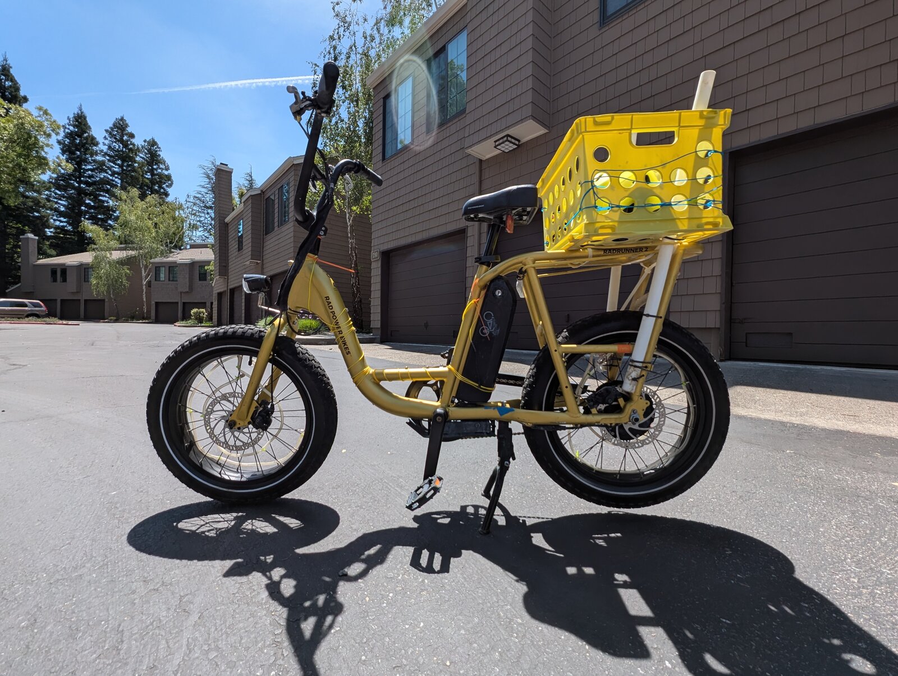
assets/photos/Original_bike/front_back/02-bike-side-profile-wide.jpg
