ibukeev/cat_bike/assets/photos/Original_bike/front_back/03-bike-rear-rack-left-closeup.jpg

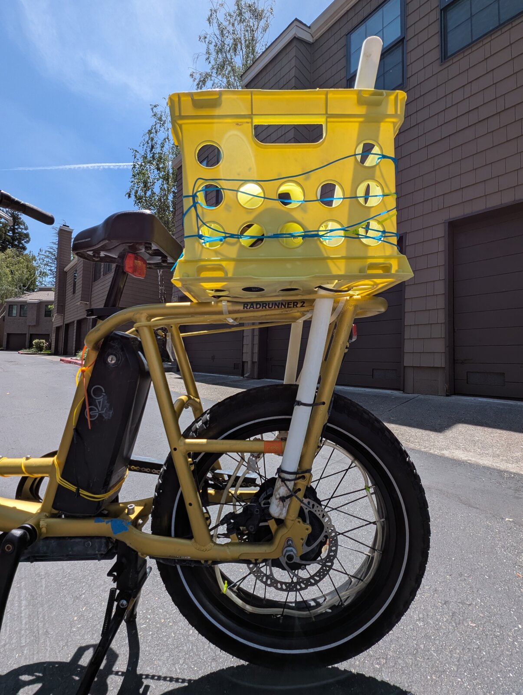
assets/photos/Original_bike/front_back/03-bike-rear-rack-left-closeup.jpg
