ibukeev/cat_bike/assets/photos/Original_bike/front_back/04-bike-rear-straight.jpg

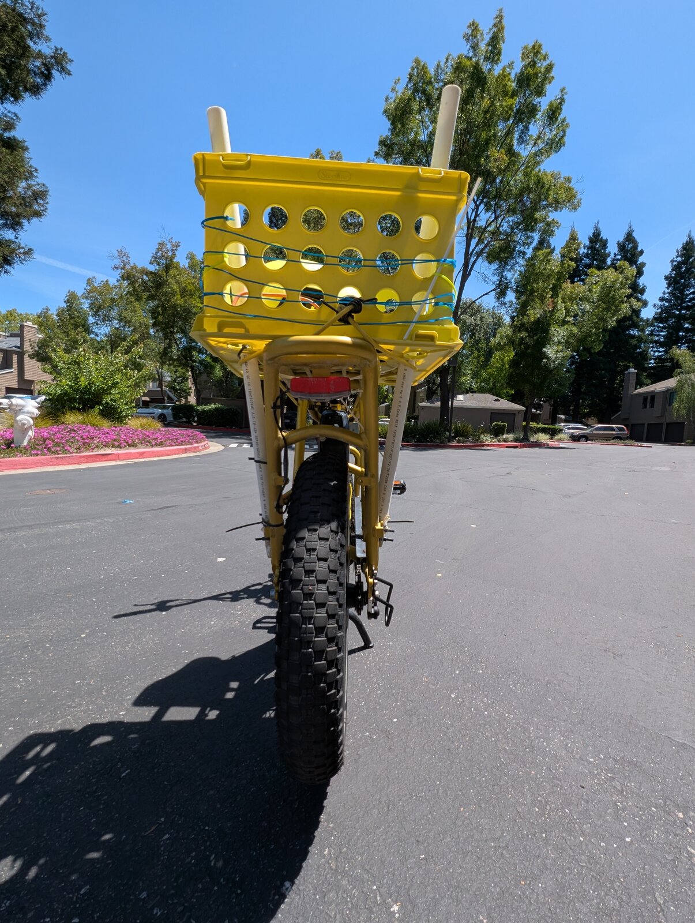
assets/photos/Original_bike/front_back/04-bike-rear-straight.jpg
