ibukeev/cat_bike/assets/photos/Original_bike/front_back/05-bike-side-profile-close.jpg

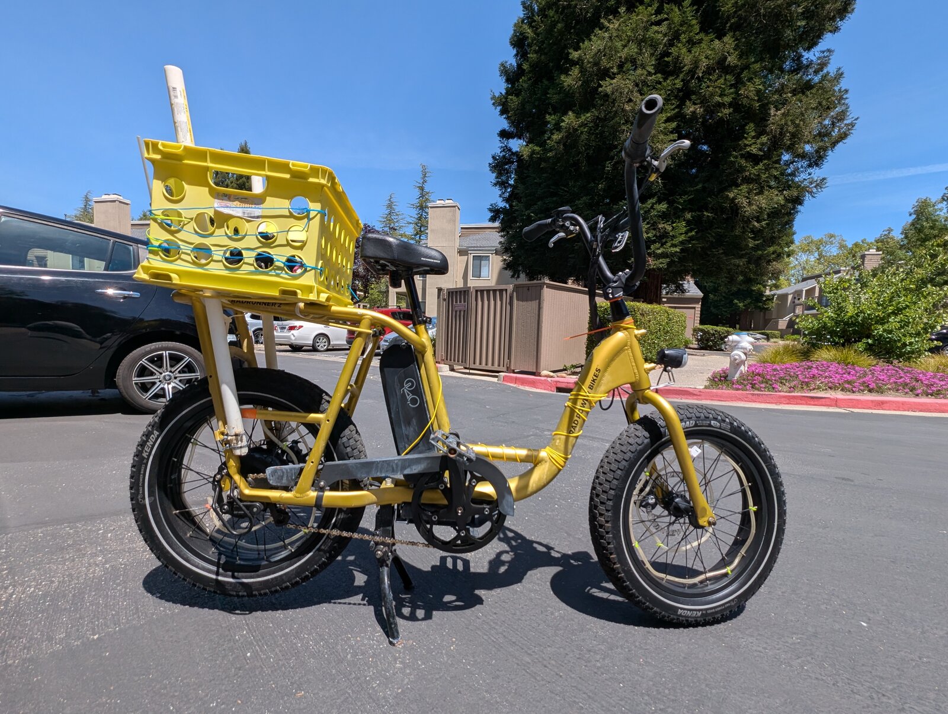
assets/photos/Original_bike/front_back/05-bike-side-profile-close.jpg
