ibukeev/cat_bike/assets/photos/Original_bike/front_back/06-bike-rear-three-quarter-close.jpg

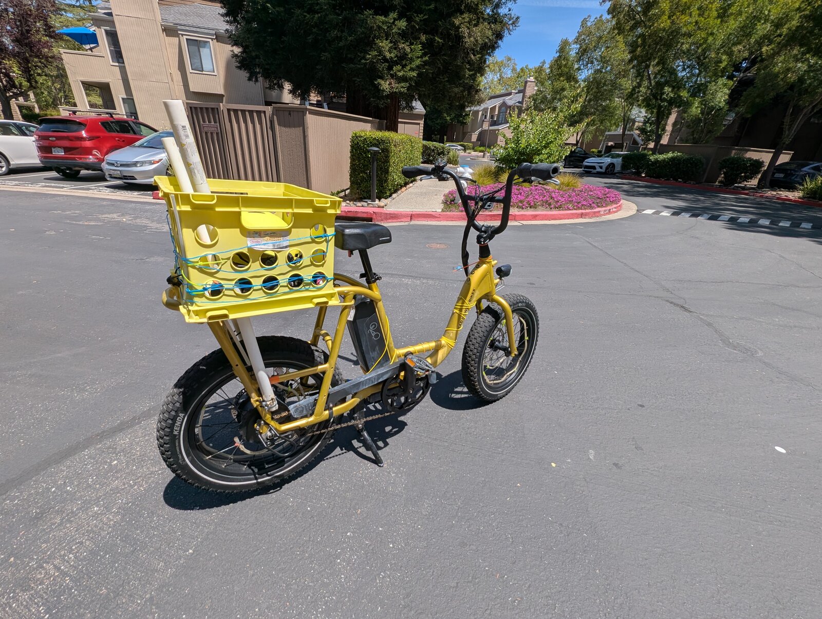
assets/photos/Original_bike/front_back/06-bike-rear-three-quarter-close.jpg
