ibukeev/cat_bike/assets/photos/Original_bike/front_back/07-bike-rear-three-quarter-wide.jpg

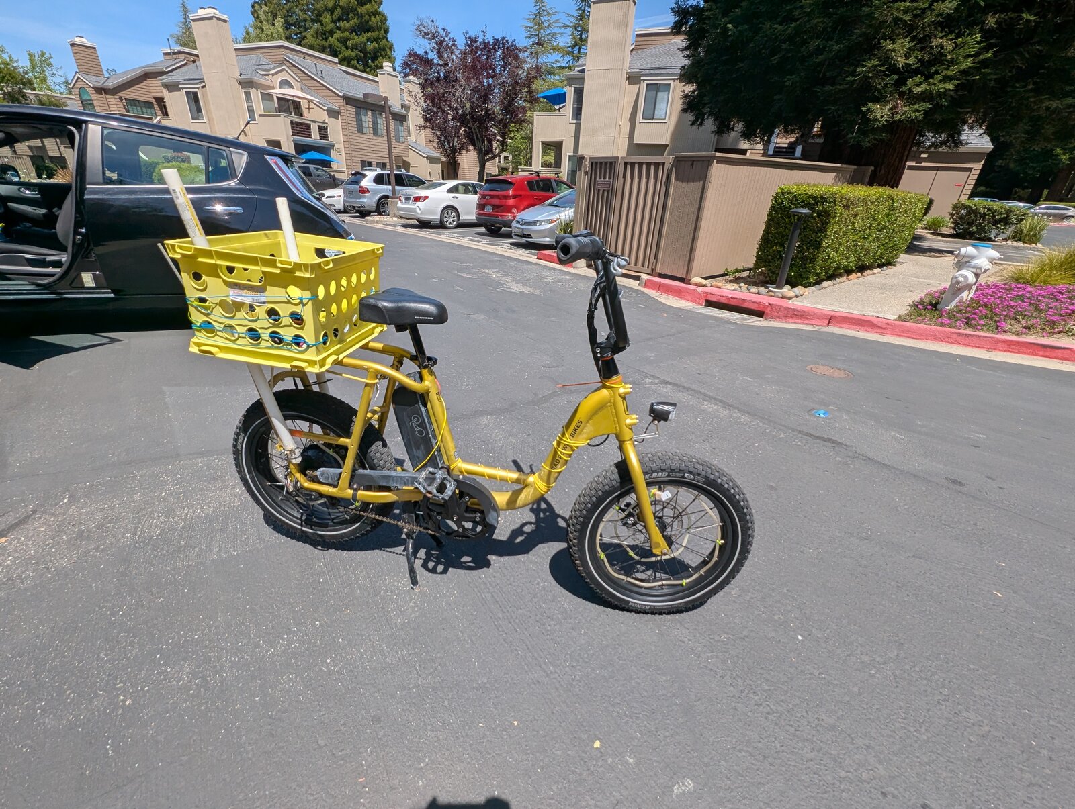
assets/photos/Original_bike/front_back/07-bike-rear-three-quarter-wide.jpg
