ibukeev/cat_bike/assets/photos/Original_bike/front_back/08-bike-front-top-handlebar-head-tube.jpg

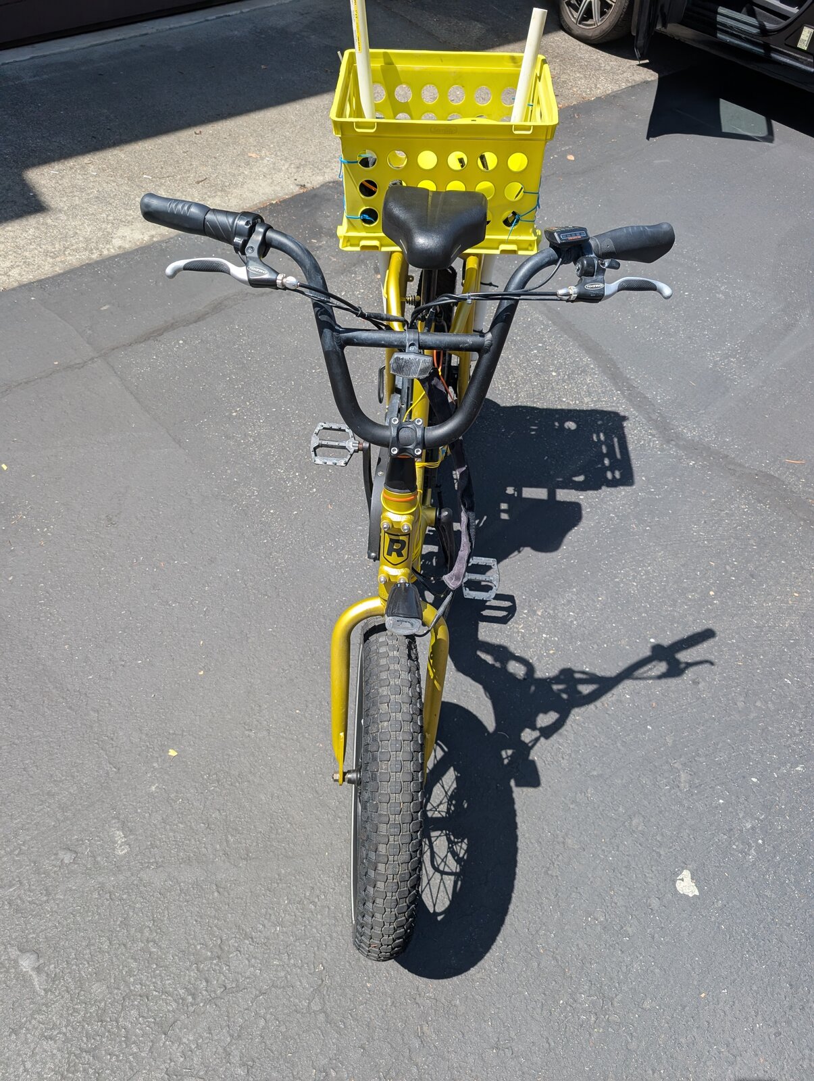
assets/photos/Original_bike/front_back/08-bike-front-top-handlebar-head-tube.jpg
