ibukeev/cat_bike/assets/photos/Original_bike/Random/PXL_20240818_203511223.jpg

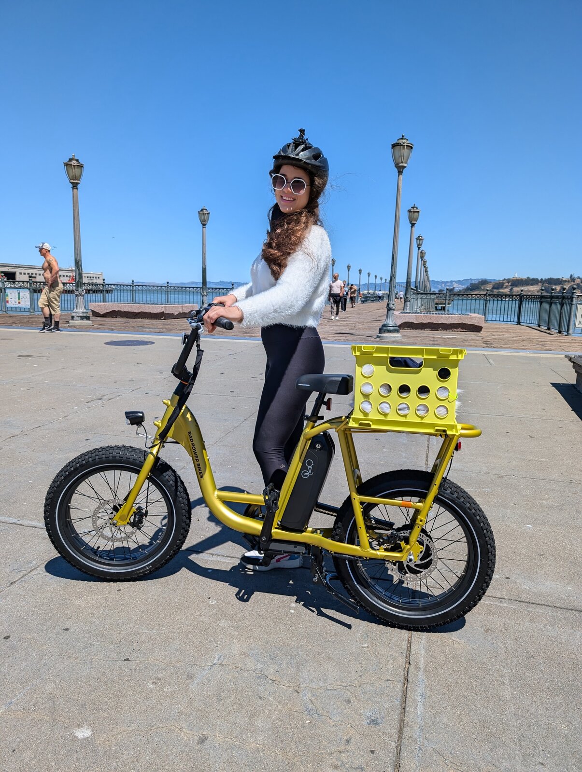
assets/photos/Original_bike/Random/PXL_20240818_203511223.jpg
