ibukeev/cat_bike/assets/photos/Original_bike/Random/PXL_20250420_212913223.jpg

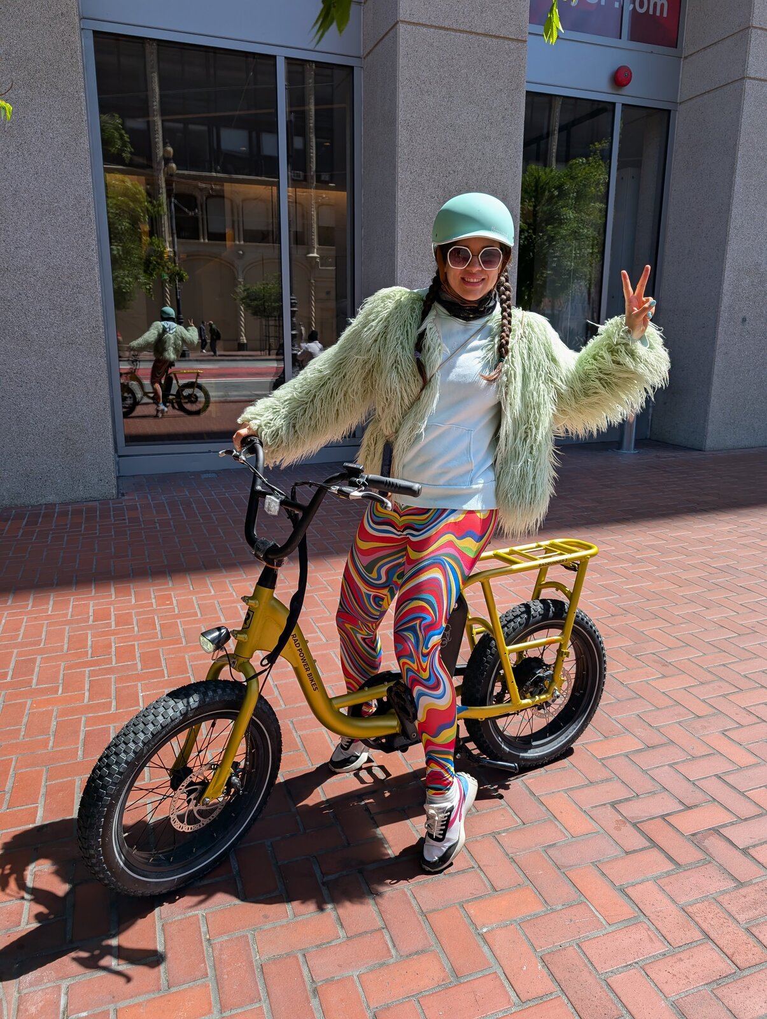
assets/photos/Original_bike/Random/PXL_20250420_212913223.jpg
