ibukeev/cat_bike/assets/photos/Original_bike/Random/Screenshot_2024-07-29_163031_400x.webp

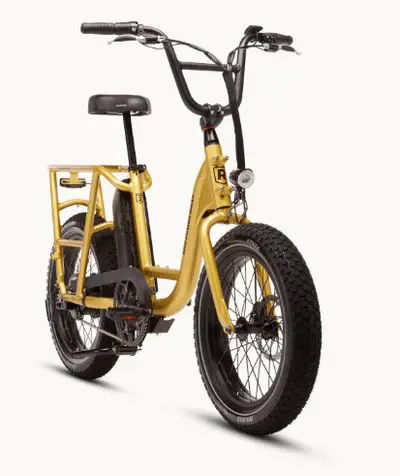
assets/photos/Original_bike/Random/Screenshot_2024-07-29_163031_400x.webp
