ibukeev/cat_bike/assets/references/cat-head/cat-head-reference-v1.png

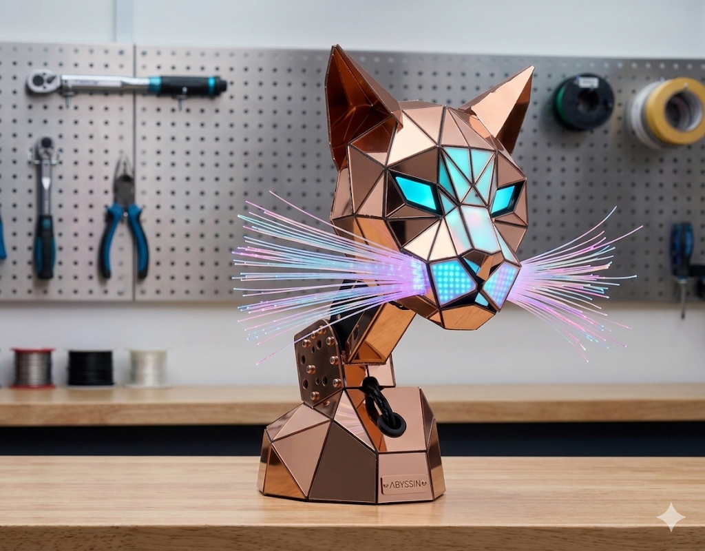
assets/references/cat-head/cat-head-reference-v1.png
