ibukeev/cat_bike/assets/references/cat-head/cat-head-reference-v2.png

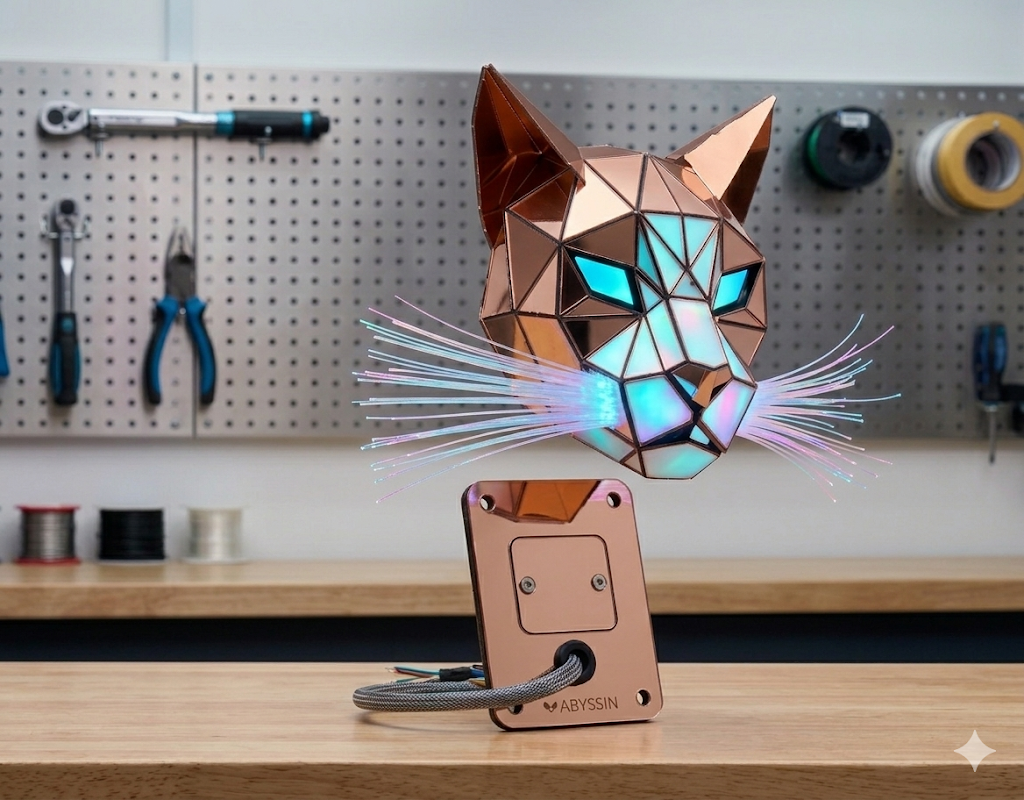
assets/references/cat-head/cat-head-reference-v2.png
