ibukeev/cat_bike/assets/references/cat-head/cat-head-reference-v3.png

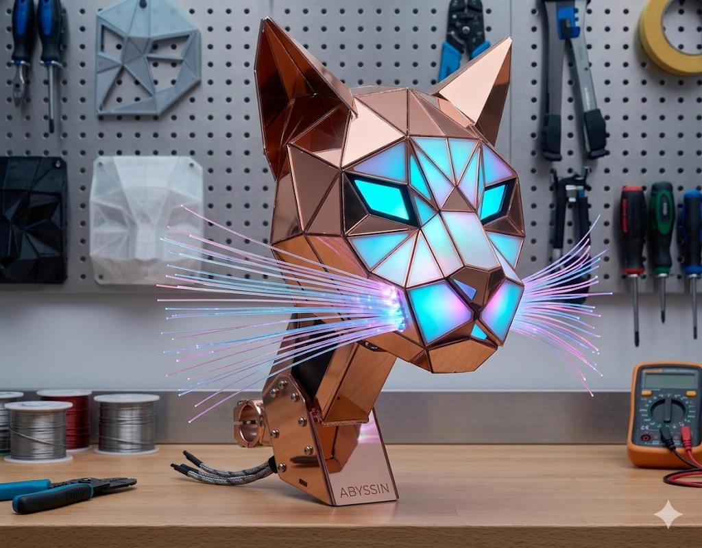
assets/references/cat-head/cat-head-reference-v3.png
