ibukeev/cat_bike/assets/references/cat-head/cat-head-reference-v4.png

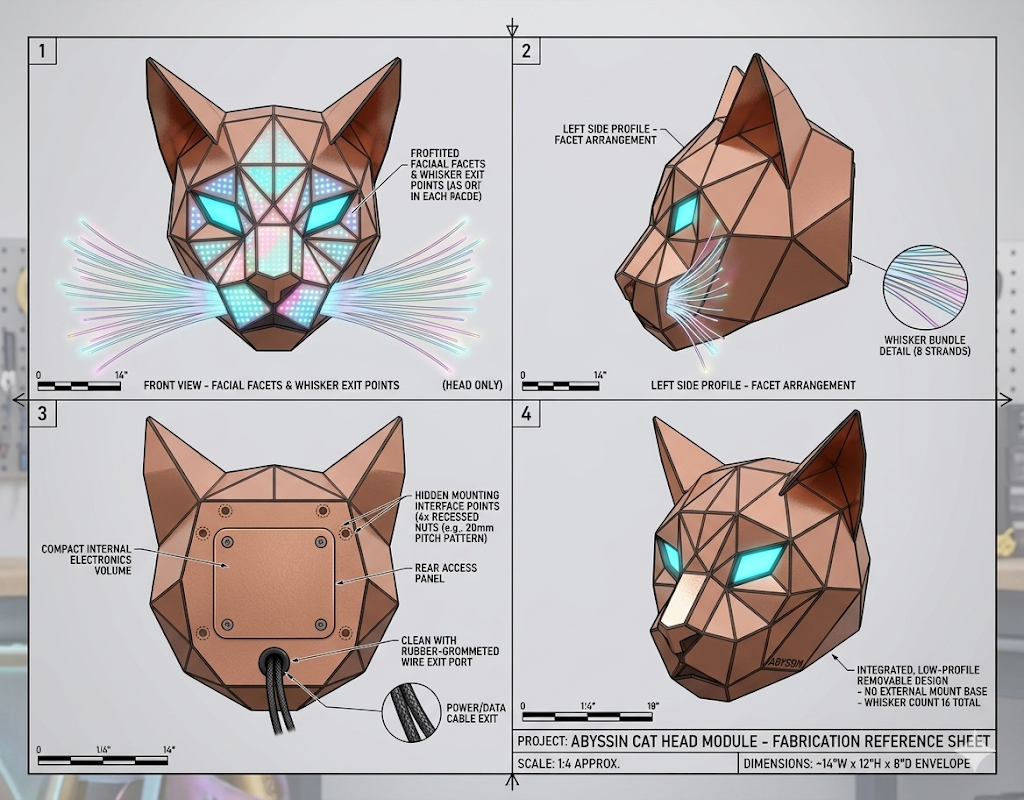
assets/references/cat-head/cat-head-reference-v4.png
