ibukeev/cat_bike/assets/references/cat-head/Gemini_Generated_Image_orxfnrorxfnrorxf.png

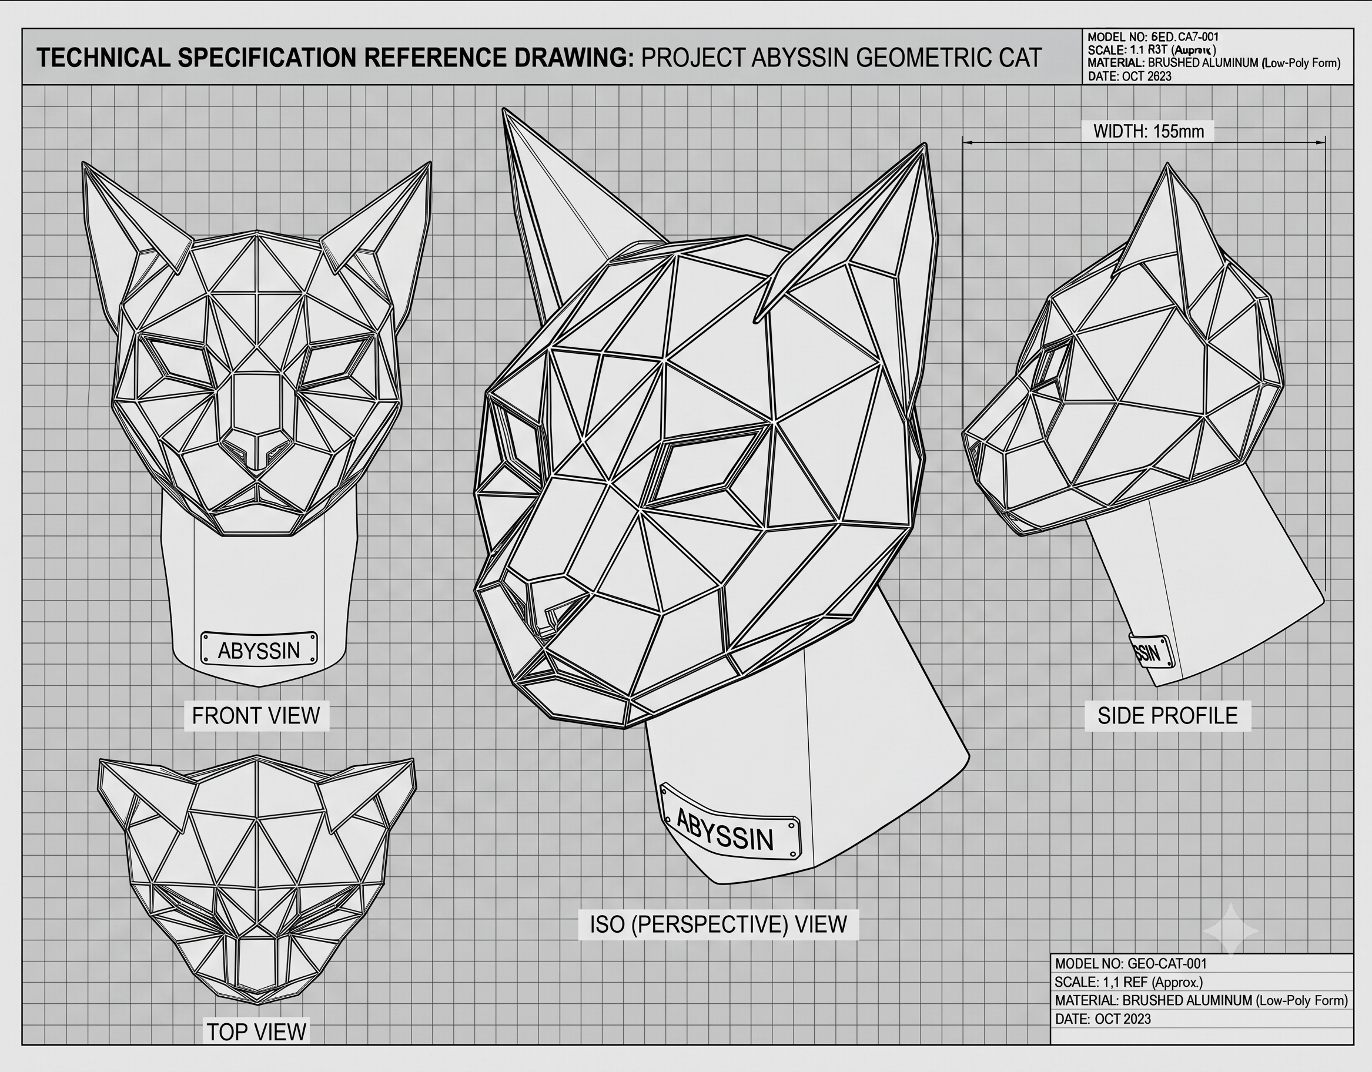
assets/references/cat-head/Gemini_Generated_Image_orxfnrorxfnrorxf.png
