ibukeev/cat_bike/hardware/mechanical/fabrication/3d-print/cat-head-full-size-v1/output/10-design-gates/gate2-section-layout/gate2-section-review.png

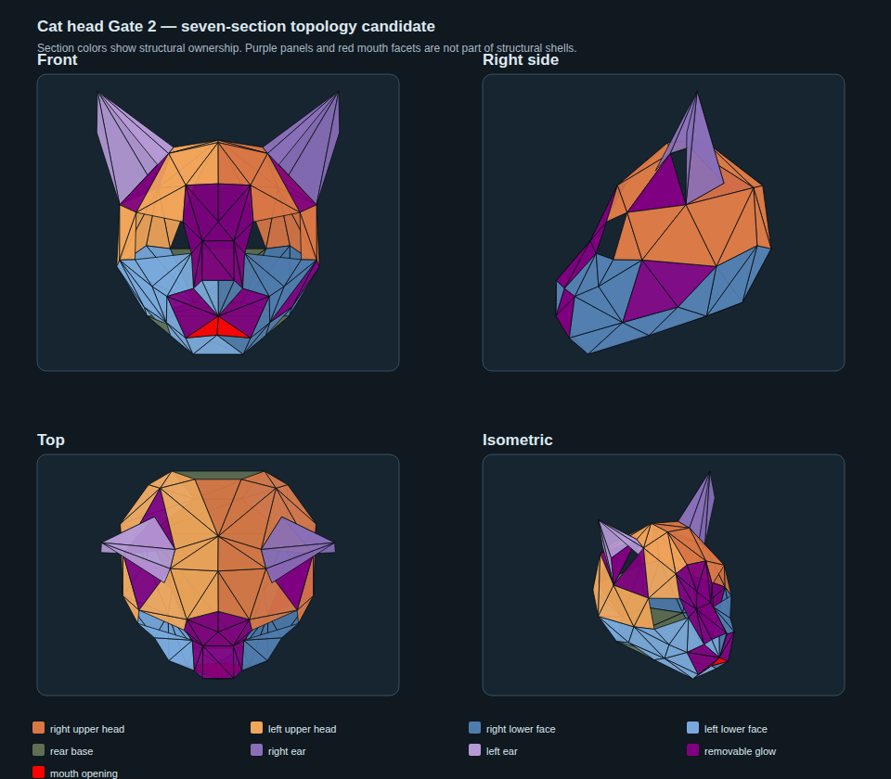
hardware/mechanical/fabrication/3d-print/cat-head-full-size-v1/output/10-design-gates/gate2-section-layout/gate2-section-review.png
