ibukeev/cat_bike/hardware/mechanical/fabrication/3d-print/cat-head-full-size-v1/output/10-design-gates/gate3-structural-shells/gate3-shells-rear.png

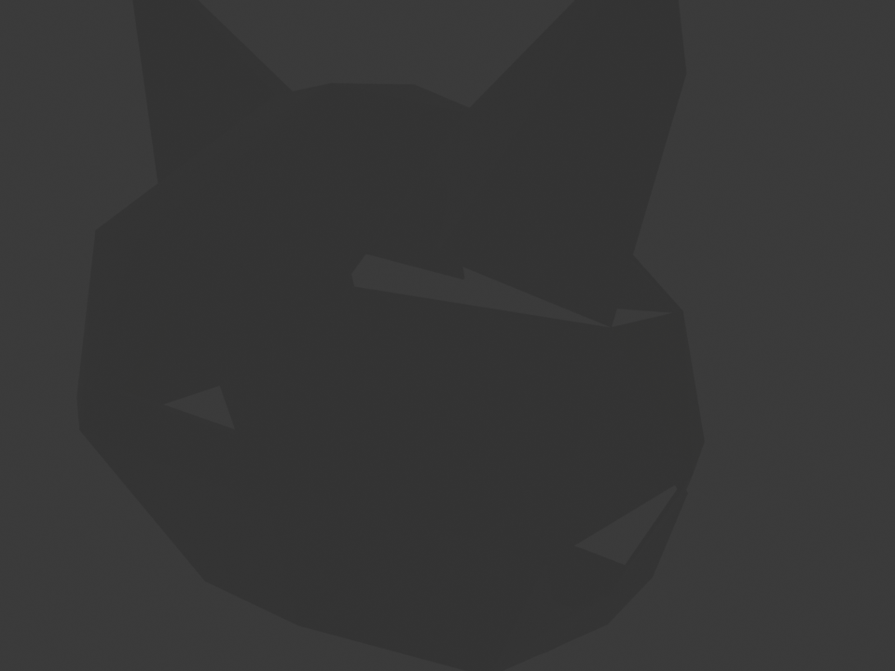
hardware/mechanical/fabrication/3d-print/cat-head-full-size-v1/output/10-design-gates/gate3-structural-shells/gate3-shells-rear.png
