ibukeev/cat_bike/hardware/mechanical/fabrication/3d-print/cat-head-full-size-v1/output/10-design-gates/gate5-ribs-and-joints/TMP/Pasted image (2).png

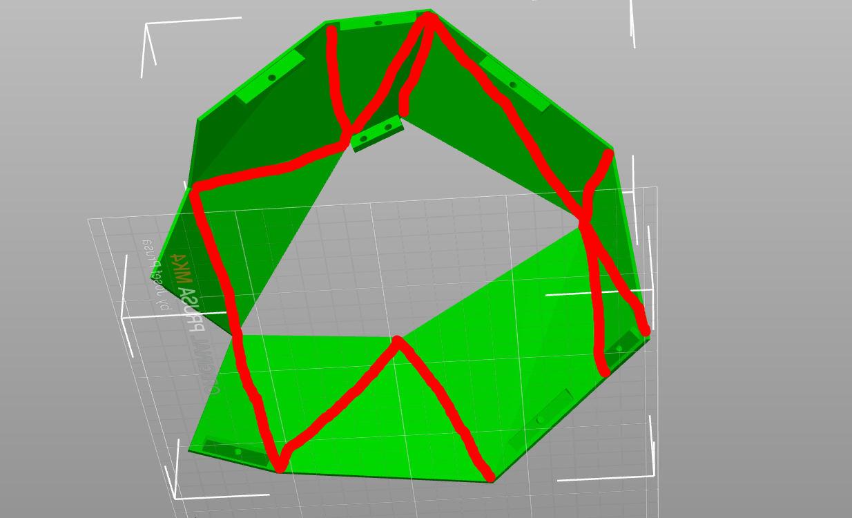
hardware/mechanical/fabrication/3d-print/cat-head-full-size-v1/output/10-design-gates/gate5-ribs-and-joints/TMP/Pasted image (2).png
