ibukeev/cat_bike/hardware/mechanical/fabrication/3d-print/controller-box-v1-printed-base/output/controller-box-v1-flat-base-proposal-bottom.png

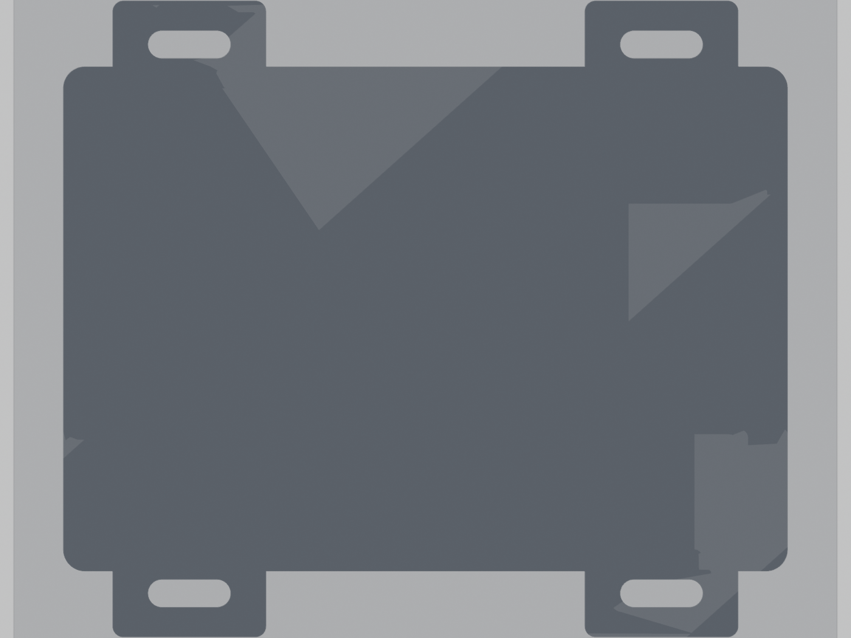
hardware/mechanical/fabrication/3d-print/controller-box-v1-printed-base/output/controller-box-v1-flat-base-proposal-bottom.png
