ibukeev/cat_bike/hardware/mechanical/fabrication/metal/cat-head-frame-fixed-mount-v0/output/v04-finalized-interface/flat-plates/head-rear-backplate-v04.dxf

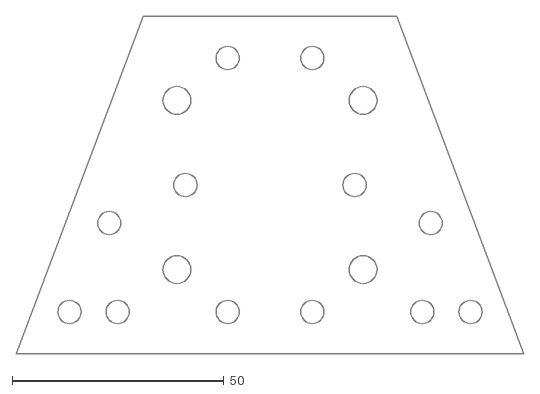
[picture p64: CAD file, 2026-09-11]
hardware/mechanical/fabrication/metal/cat-head-frame-fixed-mount-v0/output/v04-finalized-interface/flat-plates/head-rear-backplate-v04.dxf
120.0 x 79.7
