ibukeev/cat_bike/hardware/mechanical/fabrication/metal/cat-head-frame-fixed-mount-v0/output/v05-m2-coordinated-centers/flat-plates/head-rear-backplate-v05.dxf

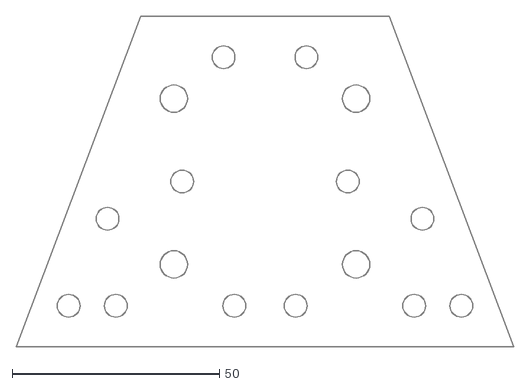
[picture p65: CAD file, 2026-09-11]
hardware/mechanical/fabrication/metal/cat-head-frame-fixed-mount-v0/output/v05-m2-coordinated-centers/flat-plates/head-rear-backplate-v05.dxf
120.0 x 79.7
