ibukeev/cat_bike/hardware/mechanical/fabrication/templates/cat-head-cardboard-fabrication-v1/assembly/accepted-panels-3d.obj

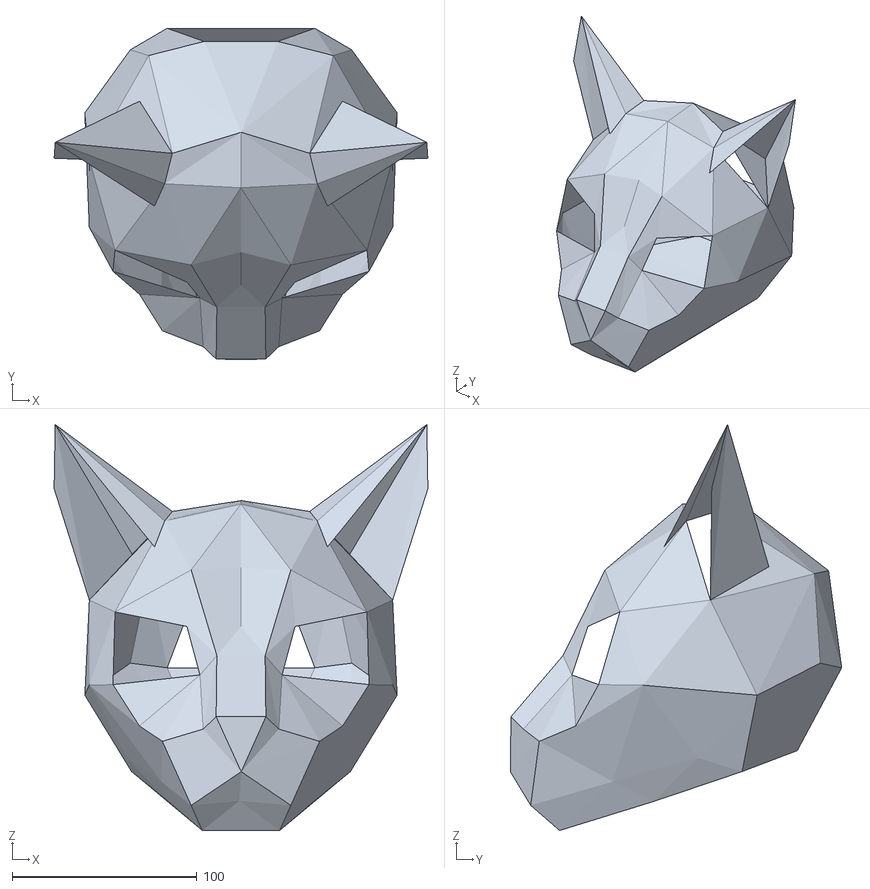
[picture p66: CAD file, 2026-07-14]
hardware/mechanical/fabrication/templates/cat-head-cardboard-fabrication-v1/assembly/accepted-panels-3d.obj
202.6 x 179.6 x 220.0
