ibukeev/cat_bike/hardware/mechanical/fabrication/templates/cat-head-wireframe-prototype/versions/v1-shape-approved-cardboard-prototype/panel-candidates/candidate-panels-3d.obj

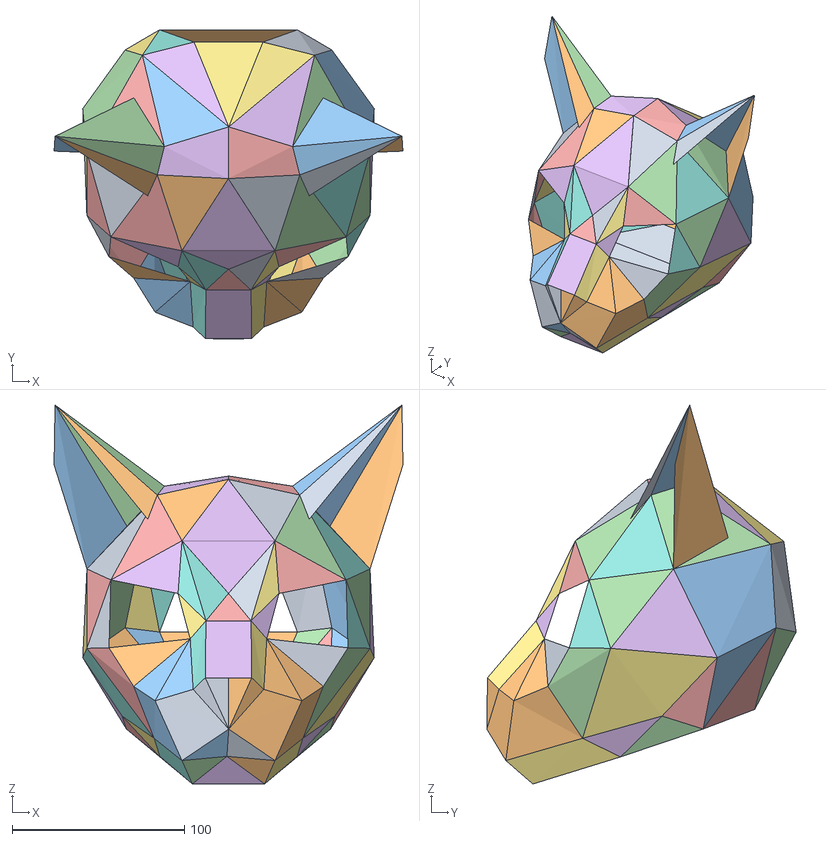
[picture p67: CAD file, 2026-07-14]
hardware/mechanical/fabrication/templates/cat-head-wireframe-prototype/versions/v1-shape-approved-cardboard-prototype/panel-candidates/candidate-panels-3d.obj
202.6 x 179.6 x 220.0
panel_MANQ008_P057_P031_P005_P035
panel_MANQ006_P070_P063_P060_P072
panel_QUAD018_P021_P026_P067_P071
panel_QUAD032_P050_P052_P064_P062
panel_QUAD021_P026_P067_P028_P069
panel_QUAD035_P052_P064_P054_P066
panel_QUAD017_P020_P021_P032_P030
panel_QUAD031_P049_P050_P058_P056
panel_MANQ007_P072_P060_P057_P031
panel_QUAD008_P007_P025_P026_P069
panel_QUAD025_P037_P051_P052_P066
panel_QUAD019_P026_P027_P028_P067
panel_QUAD033_P052_P053_P054_P064
panel_QUAD010_P009_P010_P039_P022
panel_QUAD020_P026_P027_P028_P069
panel_QUAD034_P052_P053_P054_P066
panel_QUAD036_P067_P068_P070_P071
panel_QUAD013_P012_P013_P030_P014
panel_QUAD027_P041_P042_P056_P043
panel_QUAD014_P014_P017_P020_P030
panel_QUAD028_P043_P046_P049_P056
panel_MANQ001_P033_P001_P002_P034
panel_QUAD006_P005_P013_P030_P029
panel_QUAD023_P035_P042_P056_P055
panel_QUAD005_P003_P040_P041_P042
panel_QUAD003_P003_P011_P012_P013
panel_MANQ003_P024_P010_P027_P028
panel_MANQ002_P024_P010_P053_P054
panel_QUAD011_P010_P024_P028_P027
panel_QUAD012_P010_P024_P054_P053
panel_QUAD001_P001_P002_P011_P015
panel_QUAD022_P033_P034_P040_P044
panel_QUAD004_P003_P040_P034_P059
panel_QUAD002_P002_P011_P003_P059
panel_TRI012_P007_P028_P069
panel_TRI045_P037_P054_P066
panel_TRI040_P031_P071_P072
panel_TRI028_P020_P021_P026
panel_TRI056_P049_P050_P052
panel_TRI027_P016_P026_P027
panel_TRI055_P045_P052_P053
panel_TRI059_P050_P060_P062
panel_TRI034_P024_P054_P064
panel_TRI016_P009_P016_P027
panel_TRI047_P039_P045_P053
panel_TRI033_P024_P028_P067
panel_TRI036_P024_P065_P068
panel_TRI058_P050_P057_P060
panel_TRI014_P009_P010_P027
panel_TRI019_P010_P039_P053
panel_TRI030_P021_P031_P071
panel_TRI026_P016_P020_P026
panel_TRI054_P045_P049_P052
panel_TRI035_P024_P064_P065
panel_TRI037_P024_P067_P068
panel_TRI064_P063_P064_P065
panel_TRI010_P007_P008_P027
panel_TRI043_P037_P038_P053
panel_TRI011_P007_P027_P028
panel_TRI044_P037_P053_P054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
