ibukeev/cat_bike/hardware/mechanical/fabrication/templates/cat-head-wireframe-prototype/versions/v1-shape-approved-cardboard-prototype/panel-candidates/eye-insert-panels.obj

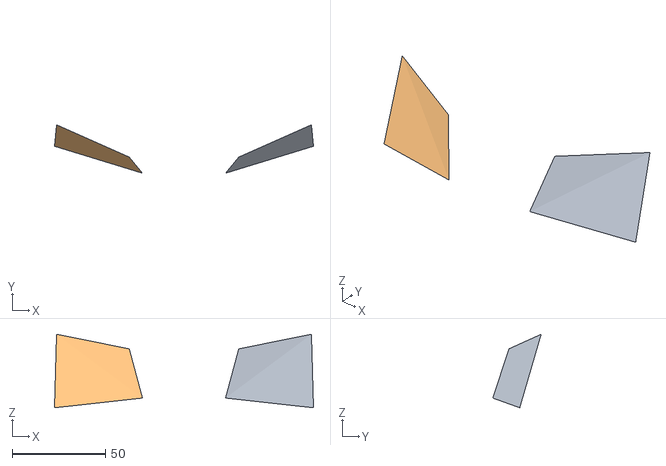
[picture p68: CAD file, 2026-07-14]
hardware/mechanical/fabrication/templates/cat-head-wireframe-prototype/versions/v1-shape-approved-cardboard-prototype/panel-candidates/eye-insert-panels.obj
138.8 x 25.9 x 39.4
insert_INSERT_EYE_RIGHT_P015_P017_P016_P019
insert_INSERT_EYE_LEFT_P044_P046_P045_P048
