ibukeev/cat_bike/hardware/mechanical/fabrication/3d-print/cat-head-full-size-v1/output/FINAL_PRINT_SET/README.md

# Selected large-head print records

Pruned on 2026-09-10. Retained release decisions are historical, not a new
whole-head manufacturing approval. The user is rebuilding the large head.

- [Bilateral V3 eye release](01-eye-modules/v3-corner-repair-release-v1/README.md):
  approved eye-module package, separate STLs, CAD and saved Both_eyes_PRINT_V1.3mf.
- [Right-lower V4](02-lower-right-connectors/lower-right-connector-integration-v4/README.md):
  selected connector release, including the Ilya manual CAD edit and 3MF companion.
- [Left-lower manual master](03-lower-left-connectors/left-lower-manual-master-v1/README.md):
  the user-designated CAD master and corresponding 3MF, unchanged.
- [Later selected lower-shell print records](../../working/README.md):
  retained 0.25 mm voxel-union meshes and slicer projects.

Rejected/withheld right-lower V1–V3 releases, backups and obsolete top-level
checksum/index files were retired. Remaining per-release manifests/checksums
are original provenance; see [the cleanup hash inventory](../../RETAINED_FILES.json)
for the exact bytes retained today, including subsequent manual edits.

There is no approved complete large-head print set. Older retracted head
packages and physically failed V1 eye carriers are in local recovery only.
