ibukeev/cat_bike/hardware/mechanical/fabrication/3d-print/cat-head-full-size-v1/output/FINAL_PRINT_SET/03-lower-left-connectors/README.md

# Lower-left connector master

Current user-designated master:

`left-lower-manual-master-v1/LEFT_LOWER_COMPLETE_OPAQUE_UNION_WITH_CONNECTORS_V1.FCStd`

Do not use earlier review, reconstructed, automated-union, or whole-assembly
mirror files as the source for future left-lower work.
