ibukeev/cat_bike/hardware/mechanical/fabrication/3d-print/cat-head-full-size-v1/output/70-freecad-pilots/opposite-side-flange-pilot-v1/right-upper-as-printed-working-assembly-v1/README.md

# Selected working assemblies

- RIGHT_UPPER_AS_PRINTED_WORKING_ASSEMBLY_V6.FCStd: latest documented working
  snapshot. Despite the filename, it includes shared whole-head context.
- RIGHT_UPPER_AS_PRINTED_WORKING_ASSEMBLY_V5.FCStd: preserve for socket/root
  recovery; prior V6 cleanup removed important geometry.
- RIGHT_UPPER_AS_PRINTED_WORKING_ASSEMBLY_V2.FCStd: editable source of the
  selected left/right lower-shell working print packages.

V1, V3, V4, unnamed copies, automatic backups and TEST.3mf were retired to the
2026-09-10 large-head recovery archive. The stopped missing-socket trial
RIGHT_TOP_PRINT.3mf was also retired. RIGHT_TOP_PRINT_2.3mf and assembly.3mf
are retained user companions, not newly approved print jobs.

The remaining STL companions and original assembly-validation.json are historical
records; that early validation does not certify later manually edited V2/V5/V6.
No retained CAD, mesh or slicer file was changed during cleanup.

Start at [the rebuild index](../../../../README.md). Do not overwrite these snapshots.
