ibukeev/cat_bike/hardware/mechanical/fabrication/3d-print/cat-head-full-size-v1/output/70-freecad-pilots/opposite-side-flange-pilot-v1/right-upper-as-printed-working-assembly-v1/CHECKPOINT_2026-08-21.md

# RIGHT Upper As-Printed Working Assembly V1 Checkpoint — 2026-08-21

## Decision

The user approved the exact current V34 RIGHT-upper recovery baseline:

`../right-upper-c009-deletion-review-v34/CAT_HEAD_RIGHT_UPPER_C009_DELETION_REVIEW_V34.FCStd`

V34 SHA-256:

`9cf0b72f711c8f0eb15d8825e430e9bf6ec0dc9611ac7c297b90fafa9b554584`

The user then authorized creation of one FreeCAD file to work from using the
printed lower parts, printed opaque eye parts, approved translucent-eye CAD
context, approved ears, and current aluminum coordination datums.

## Created working file

`RIGHT_UPPER_AS_PRINTED_WORKING_ASSEMBLY_V1.FCStd`

SHA-256:

`81cd156d42afb21b829f775b735cd92e97bc863c8e58622ef215011fffc4ecc2`

Validation report:

`assembly-validation.json`

Validation SHA-256:

`9bca98d2a3a2ee1ab7144e594cd977ee6421ee8b7de8b3252a5d08ecab6e9f9b`

## Creation result

- one FreeCAD-writing session used;
- output reopened successfully;
- 41 separate V34 RIGHT-upper owner components preserved;
- 73 total shape objects present;
- no fused assembly object created;
- no LEFT-upper owner added;
- no source document saved;
- all pinned source hashes unchanged;
- no STL/3MF export or slicing performed.

## Gate

This file is a working assembly and is **not print approved**. Perform exact
collision and clearance classification before defining any upper-only geometry
correction. The frozen lower masters remain context only.
