ibukeev/cat_bike/hardware/mechanical/fabrication/3d-print/cat-head-full-size-v1/output/FINAL_PRINT_SET/02-lower-right-connectors/lower-right-connector-integration-v4/CHECKPOINT_2026-08-21.md

# Lower-right complete opaque V4 checkpoint — 2026-08-21

Status: PRINT_RELEASE_PASS__V4_ONE_COMPLETE_OPAQUE_STL_AND_THREE_TRANSLUCENT_STLS_READY

Use V4 only. V1-V3 are superseded.

- Accepted opaque owners included: 35
- Packaged opaque constituents including ledge: 36
- Opaque STL files: 1
- Translucent STL files: 3
- Reloaded opaque mesh shells: 34
- PrusaSlicer opaque manifold/parts: yes/36
- Opaque boundary/nonmanifold/degenerate/duplicate edges or facets: 0/9/0/3
- Global destructive BRep union: not used
- Invented bridges: not used
- Negative-X translucent plank: absent
- Rejected zero-area Face6: absent

Regeneration requires a fresh output identity because V4 is immutable after release. No slicing or G-code was performed.
