ibukeev/cat_bike/hardware/mechanical/fabrication/3d-print/cat-head-full-size-v1/output/00-current-review/renders/ear-root-marked-relocation-m3-through-bolt-full-head-context.png

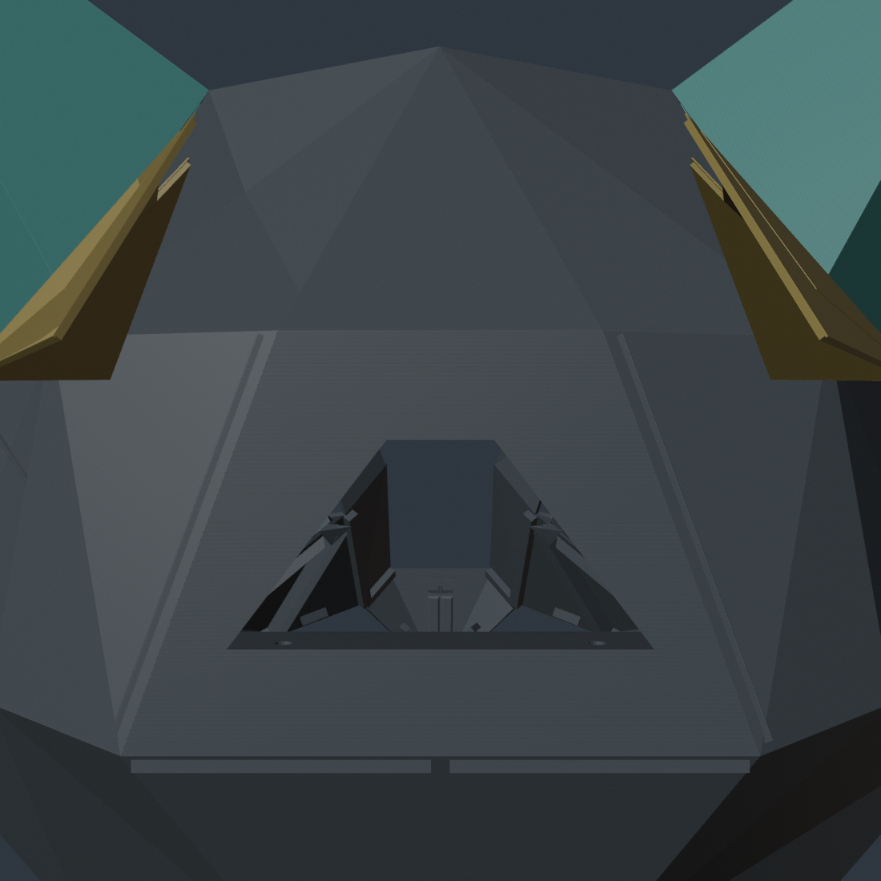
hardware/mechanical/fabrication/3d-print/cat-head-full-size-v1/output/00-current-review/renders/ear-root-marked-relocation-m3-through-bolt-full-head-context.png
