ibukeev/cat_bike/hardware/mechanical/fabrication/3d-print/cat-head-full-size-v1/output/10-design-gates/gate7-small-test-print-100mm/TMP/Pasted image.png

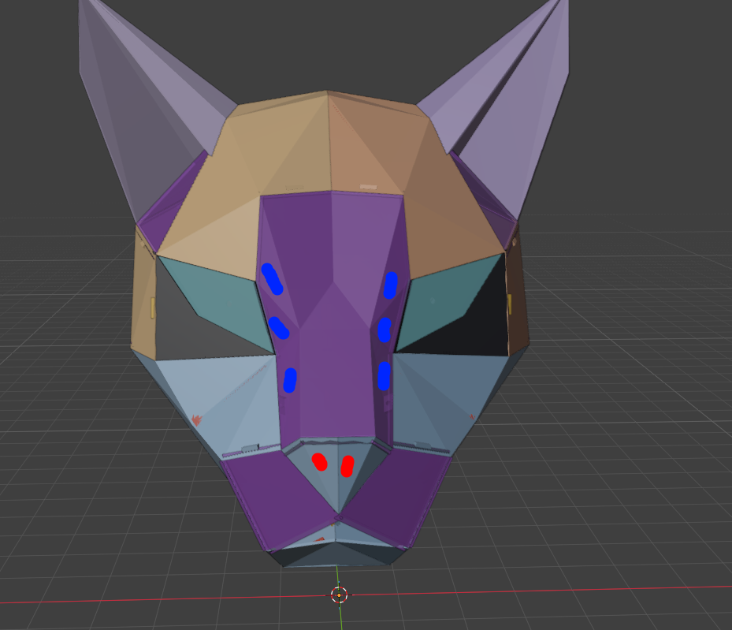
hardware/mechanical/fabrication/3d-print/cat-head-full-size-v1/output/10-design-gates/gate7-small-test-print-100mm/TMP/Pasted image.png
