ibukeev/cat_bike/hardware/mechanical/fabrication/3d-print/cat-head-full-size-v1/output/50-slicer-projects/right-upper-as-printed-10mm-brim-layout-v1/first-layer-brim-support-evidence-v1.png

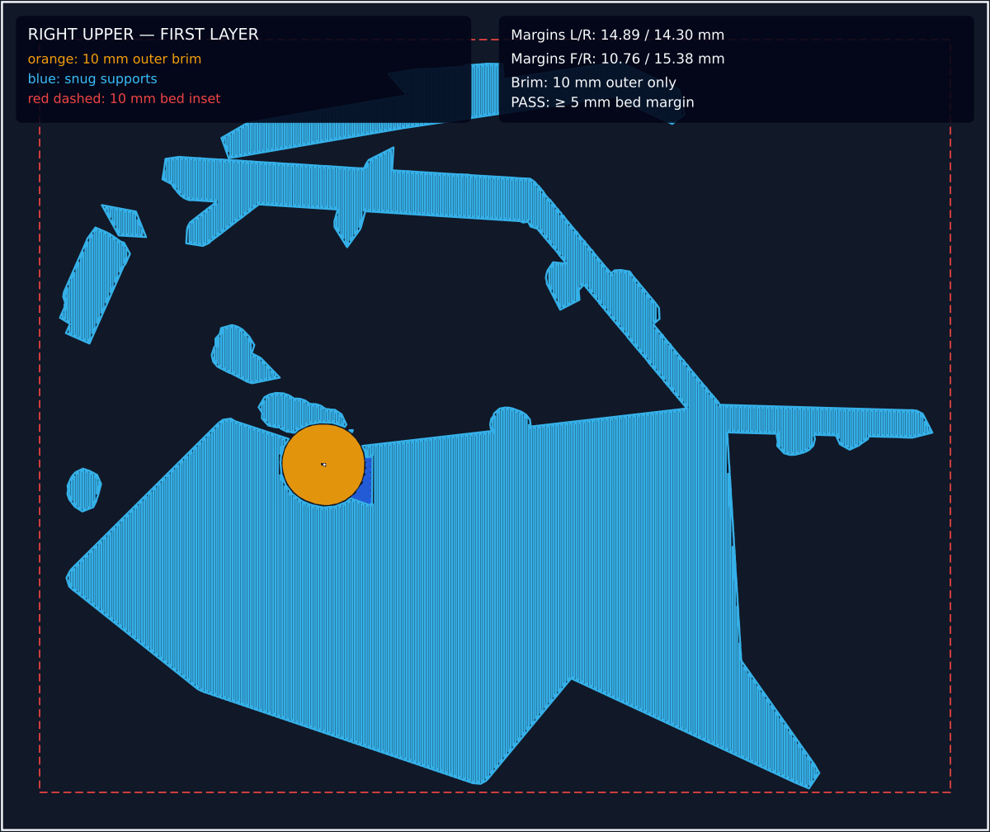
hardware/mechanical/fabrication/3d-print/cat-head-full-size-v1/output/50-slicer-projects/right-upper-as-printed-10mm-brim-layout-v1/first-layer-brim-support-evidence-v1.png
