ibukeev/cat_bike/hardware/mechanical/fabrication/3d-print/cat-head-midsize-bm-2026/releases/head-rev112/rev112-front-final-head-cut-holes.png

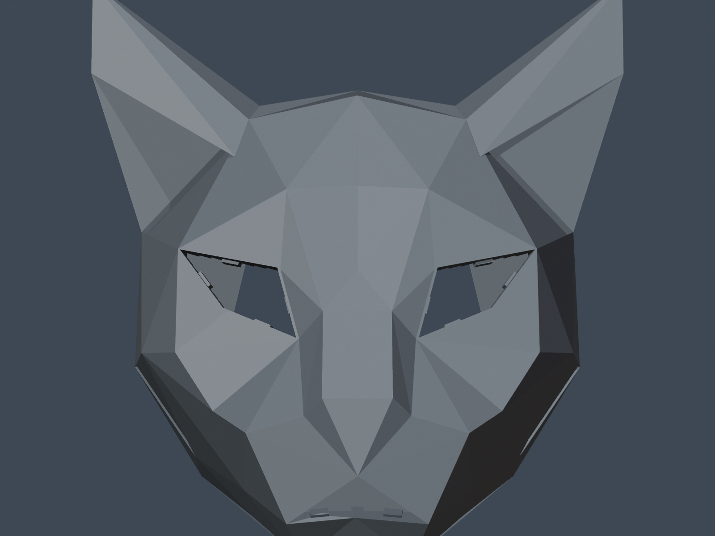
hardware/mechanical/fabrication/3d-print/cat-head-midsize-bm-2026/releases/head-rev112/rev112-front-final-head-cut-holes.png
