ibukeev/cat_bike/hardware/mechanical/fabrication/3d-print/cat-head-midsize-bm-2026/releases/mouth-rev113/rev113-isolated-mouth-halves-and-seam-only-bridge.png

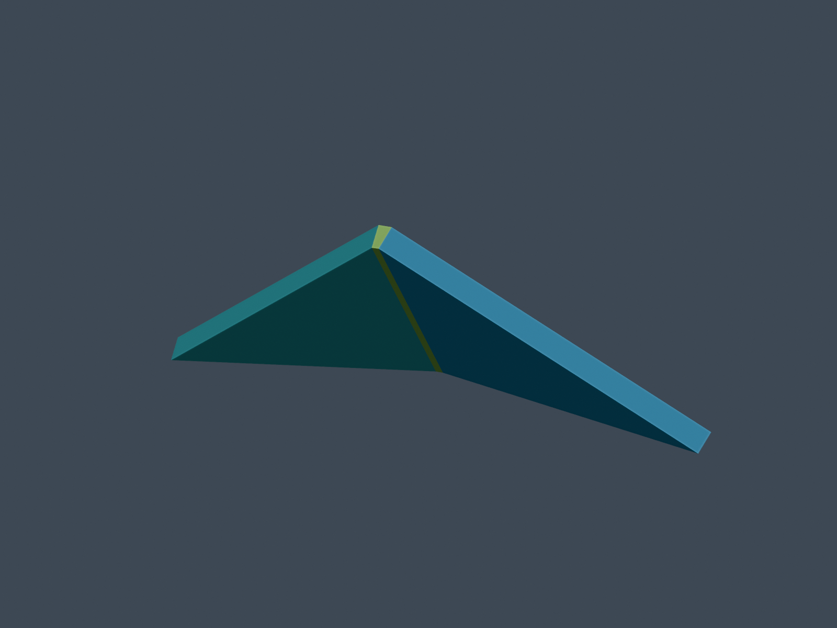
hardware/mechanical/fabrication/3d-print/cat-head-midsize-bm-2026/releases/mouth-rev113/rev113-isolated-mouth-halves-and-seam-only-bridge.png
