ibukeev/cat_bike/hardware/mechanical/fabrication/3d-print/cat-head-tiny-prototypes/single-shell-100mm/release/cat-head-100mm-shell-print-orientation.png

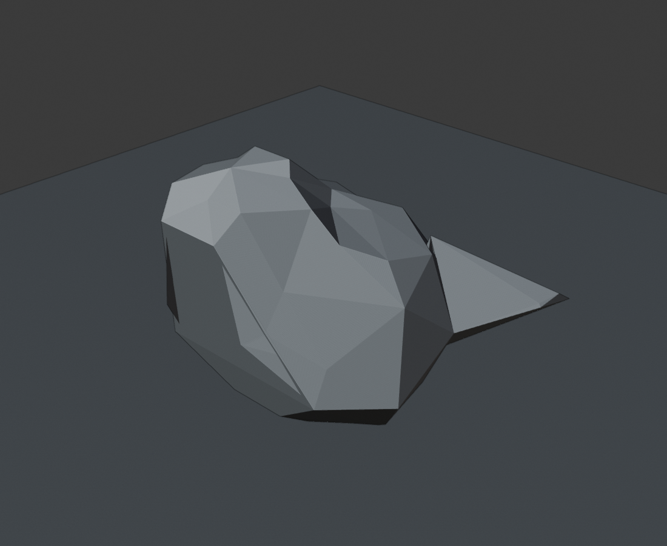
hardware/mechanical/fabrication/3d-print/cat-head-tiny-prototypes/single-shell-100mm/release/cat-head-100mm-shell-print-orientation.png
