ibukeev/cat_bike/hardware/mechanical/fabrication/3d-print/cat-head-whisker-carrier-v0/output/whisker-carrier-v0-review.png

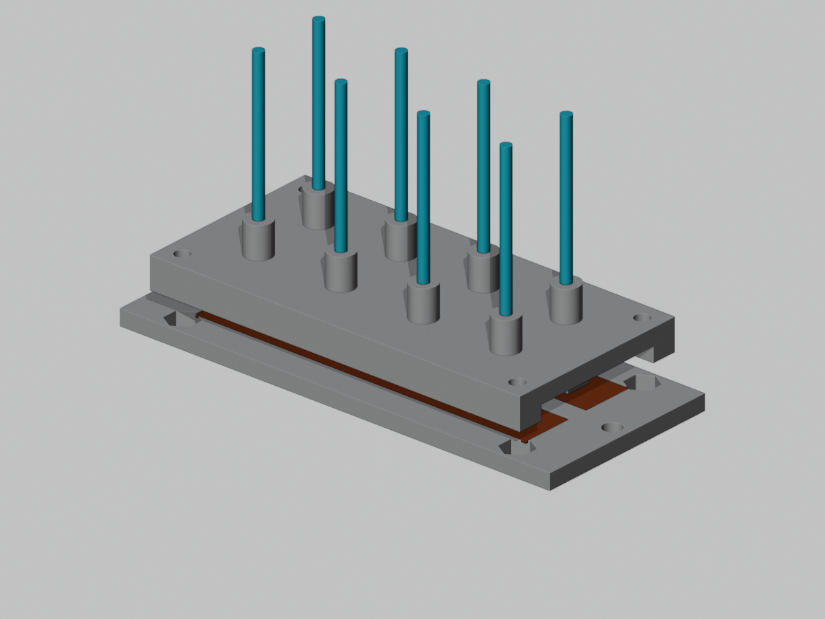
hardware/mechanical/fabrication/3d-print/cat-head-whisker-carrier-v0/output/whisker-carrier-v0-review.png
