ibukeev/cat_bike/hardware/mechanical/fabrication/metal/cat-head-frame-fixed-mount-v0/output/v04-finalized-interface/renders/v04-right-shoe-detail.png

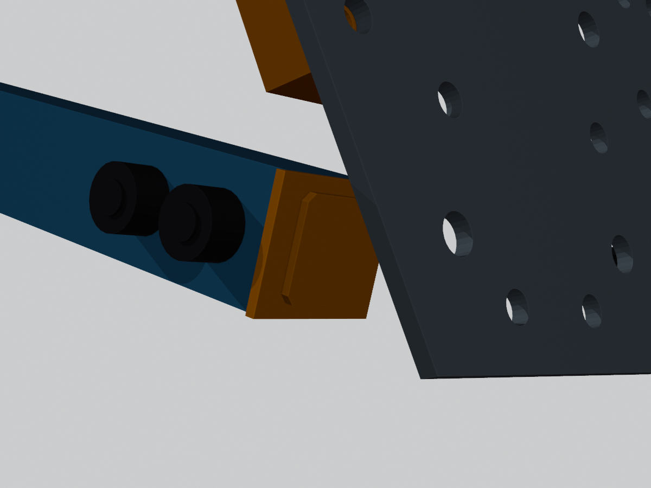
hardware/mechanical/fabrication/metal/cat-head-frame-fixed-mount-v0/output/v04-finalized-interface/renders/v04-right-shoe-detail.png
