ibukeev/cat_bike/hardware/mechanical/fabrication/metal/cat-head-frame-fixed-mount-v0/output/v04-finalized-interface/renders/v04-shell-integration-rear.png

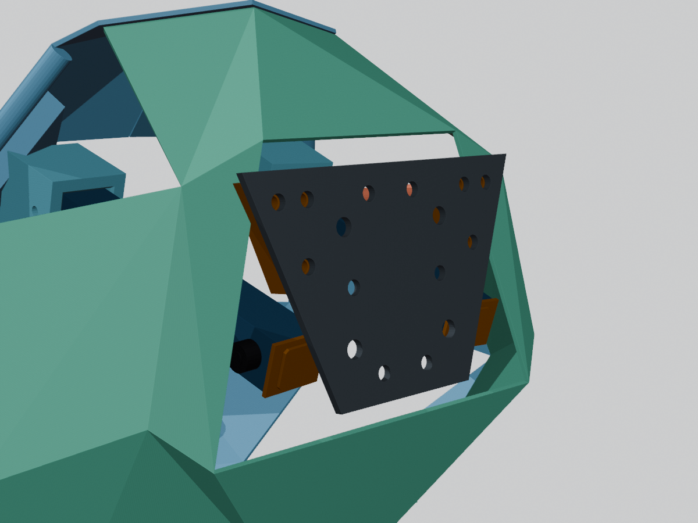
hardware/mechanical/fabrication/metal/cat-head-frame-fixed-mount-v0/output/v04-finalized-interface/renders/v04-shell-integration-rear.png
