ibukeev/cat_bike/hardware/mechanical/fabrication/metal/cat-head-frame-fixed-mount-v0/output/v04-m2-angle-stock/renders/v04-m2-angle-frame-rear.png

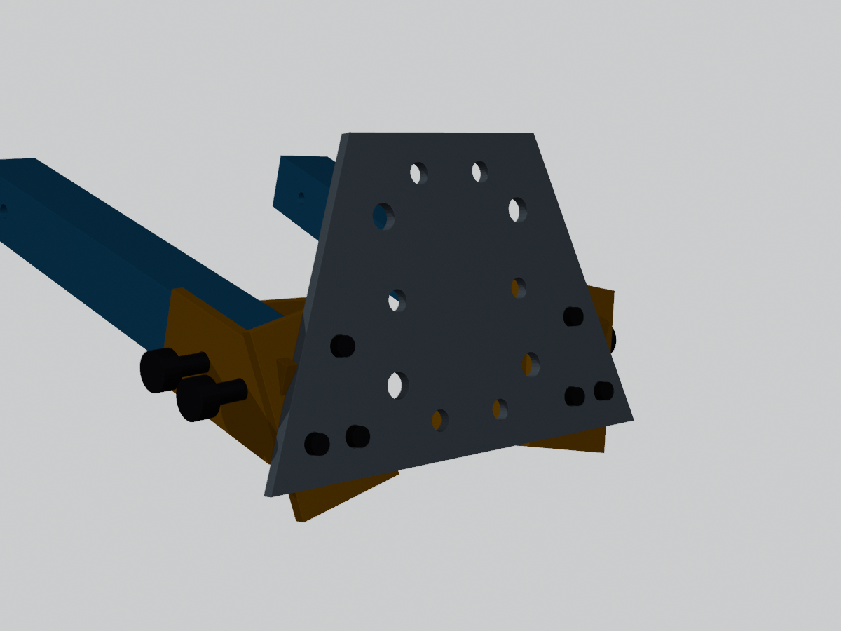
hardware/mechanical/fabrication/metal/cat-head-frame-fixed-mount-v0/output/v04-m2-angle-stock/renders/v04-m2-angle-frame-rear.png
