ibukeev/cat_bike/hardware/mechanical/fabrication/templates/cat-head-wireframe-prototype/versions/v1-shape-approved-cardboard-prototype/cad/gemini-3d-plus-symmetry-wireframe.png

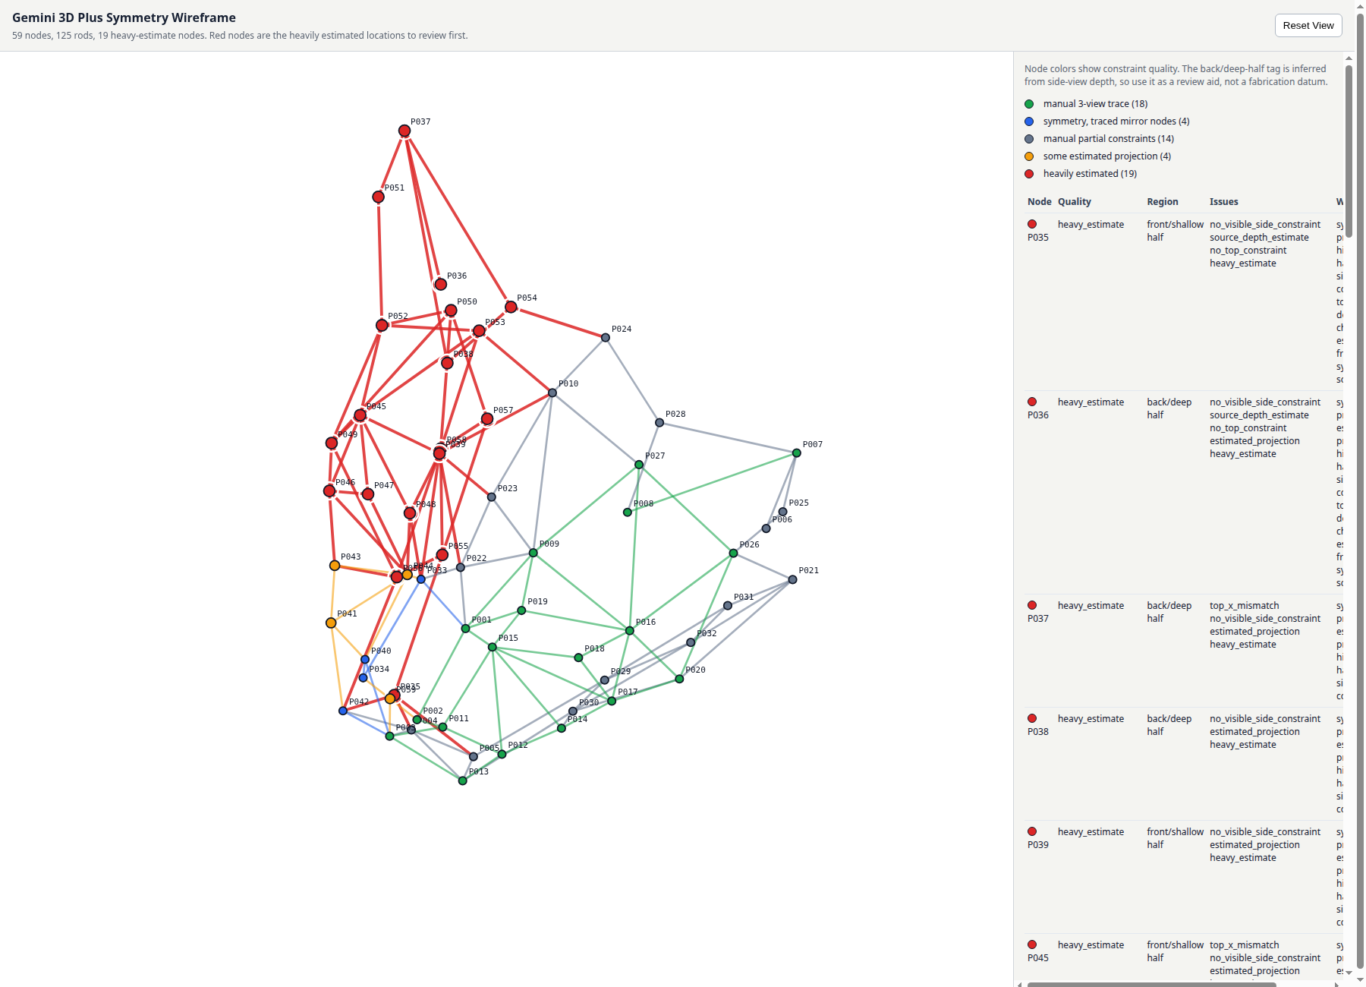
hardware/mechanical/fabrication/templates/cat-head-wireframe-prototype/versions/v1-shape-approved-cardboard-prototype/cad/gemini-3d-plus-symmetry-wireframe.png
