ibukeev/cat_bike/hardware/mechanical/fabrication/templates/cat-head-cardboard-fabrication-v1/data/validation-report.md

# Cardboard Panel Validation

Status: **PASS**

- Approved baseline: `mechanical/fabrication/templates/cat-head-wireframe-prototype/versions/v1-shape-approved-cardboard-prototype/panel-candidates/candidate-panels-3d.obj`
- Raw candidate faces: 95
- Deduplicated candidate faces: 93
- Accepted source faces: 88
- Exact triangular cardboard pieces: 115
- Excluded conflicting alternatives: 5
- Connected components: 1
- Boundary edges: 31
- Interior edges: 157
- Overused edges: 0
- Preserved eye-opening edges: 8
- Maximum flattening error: 0.000000 mm

## Excluded Alternatives

- `QUAD010`: would create a third face on P009-P010 P010-P039 P022-P039 P009-P022
- `QUAD019`: would create a third face on P027-P028 P028-P067 P026-P067
- `QUAD020`: would create a third face on P027-P028 P028-P069 P026-P069
- `QUAD033`: would create a third face on P053-P054 P054-P064 P052-P064
- `QUAD034`: would create a third face on P053-P054 P054-P066 P052-P066
