ibukeev/cat_bike/hardware/mechanical/fabrication/3d-print/cat-head-full-size-v1/output/FINAL_PRINT_SET/01-eye-modules/v3-corner-repair-release-v1/README.md

# Bilateral eye modules — V3 corner-repair print release V1

This is the current real-print eye release. It replaces the physically failed
V1 carrier STLs. Do not print the old V1 carrier files.

Each side contains one FreeCAD assembly and three independent source-coordinate
STLs: repaired carrier (including the manual mounting flange), translucent lens,
and removable LED rear plate. The left parts are exact X=0 mirrors of the approved
right parts.

No 3MF or G-code is included. Slice each STL using the actual printer/material
profile. Print the structural carrier and rear plate in opaque structural
filament; print the lens separately in natural/translucent PETG. The lens and rear
plate geometry are unchanged from the previously approved eye design.
